nThanksForAllTheFish/rd03d/docs/superpowers/plans/2026-09-07-rd03d-case.md

# RD-03D + XIAO Fusion Case Implementation Plan

> **For agentic workers:** REQUIRED SUB-SKILL: Use superpowers:subagent-driven-development (recommended) or superpowers:executing-plans to implement this plan task-by-task. Steps use checkbox (`- [ ]`) syntax for tracking.

**Goal:** Build the two-part snap-fit case (adhesive back plate + front shell with radar window and USB notch) as a native parametric design in the user's running Fusion 360, verified against the imported real board models, with STLs exported to the repo.

**Architecture:** A small MCP driver (`run_fusion.py`) sends Fusion-API Python scripts to the local Fusion MCP server (`http://127.0.0.1:27182/mcp`) and fetches viewport screenshots. Numbered build scripts create user parameters, the BackPlate component, the FrontShell component, import + position the board STEPs, run interference checks, and export STLs. Every geometry stage is verified by reading back measurements AND by viewing a screenshot (the implementer Reads the PNG — actually look at it).

**Tech Stack:** Fusion 360 API (adsk.core/adsk.fusion) over Autodesk's MCP adapter; Python stdlib driver (urllib, no deps).

**Spec:** `docs/superpowers/specs/2026-09-06-rd03d-case-design.md`

---

## Standing rules for every task in this plan

- **Sequential, single implementer.** All tasks mutate ONE live Fusion document; never parallelize.
- **Prescriptive vs adaptable:** dimensions, user parameters, feature intent, component names, and verification criteria are prescriptive. Exact Fusion API calls are the starting point — if Fusion rejects a call, consult the API docs (`fusion_mcp_read` queryType `apiDocumentation`) and adapt, keeping intent identical. Record every adaptation in your report.
- **Idempotency:** scripts guard against re-runs (check for existing parameter/component by name; delete-and-rebuild a component rather than duplicating it). If a script half-fails, fix and re-run the same script.
- **Verify visually:** after each geometry script, capture screenshots (`run_fusion.py screenshot ...`, saved under the scratchpad) and READ the image files — confirm the geometry actually looks like the design, don't just trust `success: true`.
- **Fusion API unit trap:** the API's internal length unit is **cm**. User parameters are declared in mm; `param.value` returns cm. All raw `Point3D`/extrude distances in scripts must be in cm (the scripts read `param.value` so they stay consistent — never hardcode a mm number into a Point3D).
- **Units of trust:** the design is in the user's Fusion — they can watch. Do not save/close/discard their documents; do not touch other open documents; never call `doc.close`. Saving is the user's step at the end.
- Scratchpad for screenshots: `/private/tmp/claude-501/-path-to-rd03d/1a58ef3a-b659-4aae-a07a-3f6d1a6f573b/scratchpad/case/` (create it).
- Repo working dir: /path/to/rd03d, branch `feature/rd03d-case`.
- End every commit message with:
  `Co-Authored-By: Claude Fable 5 <noreply@anthropic.com>`

## Geometry reference (all mm; origin = interior center of the case, +Z out of the wall)

- Interior: `intW`=42 × `intH`=46 × `intD`=14. Back plate face at z=0 (plate body −2..0); shell front inner face at z=14, outer at 16.
- Shell outer: 46 × 50 × 18 (wraps the plate rim: shell walls run z=−2..16).
- RD-03D bay (left): board 15.1×44.0×6.35 lying long-axis vertical, patch side facing +Z, centered at x=−11.5, y=0; board back face rests on two crossbar supports at z=6.65 so the patch face sits at z=13 (1 mm behind the front inner wall). Perimeter fence (1.5 thick, to z=11) around footprint+`boardClear`.
- XIAO bay (right): board 22.5×17.8 centered at x=+8.0, y=0 (long axis along X), USB-C pointing +X; four 3×3 corner posts `postH`=3 tall; perimeter fence to z=5 with a full opening on the +X side for the USB. Wire channel is the ~5 mm gap between the two fences.
- Radar window: front wall pocket (from outside face z=16, depth `wall`−`windowT`=0.8) over the patch end: rect x∈[−11.5−9.5, −11.5+9.5], y∈[+1, +25] (covers the top ~22 mm of the stick + margin; if board orientation checks in Task 5 show patches at −Y, mirror the window and record it).
- USB notch: through the +X wall (x∈[21,23]), from the back rim z=−2 up to z=8, width y∈[−5.7,+5.7] (10.5 plug + 2·`usbClear` ≈ 11.3).
- Snap fit: four bumps on the shell's inner ±X walls (`snapBump`=0.5 proud, 6 long, z −1.6..−0.4, crest at x=±20.5) at y=±12; the plate's ±X edges get matching 6.2-wide, 0.6-deep BLIND pockets at y=±12 spanning z −1.7..−0.3 only — material ledges above and below each pocket retain the bumps axially (0.1 z-slop per side). Plate outline = 41.7×45.7 (interior − 2·`rimGap`).
- Tape recess: plate rear face (z=−2) pocket 34×38×0.6 centered.

---

### Task 1: MCP driver + connectivity smoke test

**Files:**
- Create: `case/fusion_scripts/run_fusion.py`
- Create: `case/fusion_scripts/00_smoke.py`

- [x] **Step 1: Write the driver**

`case/fusion_scripts/run_fusion.py`:

```python
#!/usr/bin/env python3
"""Send a Fusion API script to the local Fusion MCP server, or grab a screenshot.

Usage:
  run_fusion.py script <file.py> [--read-only]
  run_fusion.py screenshot <out.png> [direction]
"""
import base64
import json
import sys
import urllib.request

URL = "http://127.0.0.1:27182/mcp"

def rpc(session, payload):
    headers = {"Content-Type": "application/json",
               "Accept": "application/json, text/event-stream"}
    if session:
        headers["MCP-Session-Id"] = session
    req = urllib.request.Request(URL, data=json.dumps(payload).encode(),
                                 headers=headers)
    with urllib.request.urlopen(req, timeout=300) as r:
        sid = r.headers.get("MCP-Session-Id", session)
        body = r.read().decode()
    return sid, (json.loads(body) if body.strip() else None)

def connect():
    sid, _ = rpc(None, {"jsonrpc": "2.0", "id": 1, "method": "initialize",
                        "params": {"protocolVersion": "2025-03-26",
                                   "capabilities": {},
                                   "clientInfo": {"name": "rd03d-case-builder",
                                                  "version": "1.0"}}})
    rpc(sid, {"jsonrpc": "2.0", "method": "notifications/initialized"})
    return sid

def call(sid, name, args):
    _, resp = rpc(sid, {"jsonrpc": "2.0", "id": 2, "method": "tools/call",
                        "params": {"name": name, "arguments": args}})
    if resp is None:
        raise SystemExit("empty MCP response")
    if "error" in resp:
        raise SystemExit(f"MCP error: {resp['error']}")
    return resp["result"].get("content", [])

def main():
    if len(sys.argv) < 3:
        raise SystemExit(__doc__)
    mode = sys.argv[1]
    sid = connect()

    if mode == "script":
        src = open(sys.argv[2]).read()
        obj = {"script": src}
        if "--read-only" in sys.argv:
            obj["readOnly"] = True
        content = call(sid, "fusion_mcp_execute",
                       {"featureType": "script", "object": obj})
        ok = True
        for c in content:
            if c.get("type") != "text":
                continue
            try:
                d = json.loads(c["text"])
                print(d.get("message", c["text"]))
                if d.get("success") is False:
                    ok = False
            except json.JSONDecodeError:
                print(c["text"])
        sys.exit(0 if ok else 1)

    if mode == "screenshot":
        out = sys.argv[2]
        args = {"queryType": "screenshot", "width": 1200, "height": 900}
        if len(sys.argv) > 3 and not sys.argv[3].startswith("--"):
            args["direction"] = sys.argv[3]
        content = call(sid, "fusion_mcp_read", args)
        for c in content:
            if c.get("type") == "image" and c.get("data"):
                open(out, "wb").write(base64.b64decode(c["data"]))
                print("saved", out)
                return
            if c.get("type") == "text":
                try:
                    d = json.loads(c["text"])
                    img = d.get("imageData") or d.get("data")
                    if img:
                        open(out, "wb").write(base64.b64decode(img))
                        print("saved", out)
                        return
                    print(c["text"][:400])
                except json.JSONDecodeError:
                    print(c["text"][:400])
        raise SystemExit("no image in response")

    raise SystemExit(__doc__)

if __name__ == "__main__":
    main()
```

(If the screenshot response format differs from both handled shapes, print the
raw content once, adapt the parser, and record the deviation.)

- [x] **Step 2: Write the smoke script**

`case/fusion_scripts/00_smoke.py`:

```python
import adsk.core

def run(_context: str):
    app = adsk.core.Application.get()
    print("Fusion", app.version)
    doc = app.activeDocument
    print("active doc:", doc.name if doc else None)
    print("open docs:", app.documents.count)
```

- [x] **Step 3: Run it**

```bash
cd case/fusion_scripts && python3 run_fusion.py script 00_smoke.py --read-only
```

Expected: `Fusion 2705...` + active doc info, exit 0. (If connection refused: Fusion or its MCP add-in isn't running — report BLOCKED, the user must have Fusion open.)

- [x] **Step 4: Commit**

```bash
git add case/fusion_scripts/run_fusion.py case/fusion_scripts/00_smoke.py
git commit -m "feat(case): Fusion MCP driver and smoke test"
```

---

### Task 2: Document + user parameters

**Files:**
- Create: `case/fusion_scripts/01_setup.py`

- [x] **Step 1: Write the setup script**

`case/fusion_scripts/01_setup.py`:

```python
import adsk.core
import adsk.fusion

PARAMS = [
    ("wall", "2 mm", "shell wall thickness"),
    ("windowT", "1.2 mm", "radar window remaining thickness"),
    ("boardClear", "0.25 mm", "clearance around boards"),
    ("usbClear", "0.4 mm", "USB cutout clearance"),
    ("tapeRecess", "0.6 mm", "adhesive tape recess depth"),
    ("backT", "2 mm", "back plate thickness"),
    ("intW", "42 mm", "interior width"),
    ("intH", "46 mm", "interior height"),
    ("intD", "14 mm", "interior depth"),
    ("rimGap", "0.15 mm", "plate-to-shell fit gap per side"),
    ("snapBump", "0.5 mm", "snap bump proudness"),
    ("radarW", "15.1 mm", "RD-03D board width"),
    ("radarH", "44.0 mm", "RD-03D board length"),
    ("radarT", "6.35 mm", "RD-03D thickness incl rear connector"),
    ("radarCx", "-11.5 mm", "radar bay center X"),
    ("xiaoW", "22.5 mm", "XIAO width incl USB overhang"),
    ("xiaoH", "17.8 mm", "XIAO depth"),
    ("xiaoCx", "8.0 mm", "XIAO bay center X"),
    ("postH", "3 mm", "XIAO post height"),
]

def run(_context: str):
    app = adsk.core.Application.get()
    des = adsk.fusion.Design.cast(app.activeProduct) if app.activeProduct else None
    if des is None:
        doc = app.documents.add(adsk.core.DocumentTypes.FusionDesignDocumentType)
        des = adsk.fusion.Design.cast(app.activeProduct)
        print("created new design document:", doc.name)
    elif (des.userParameters.itemByName("wall") is None
          and (des.rootComponent.occurrences.count > 0
               or des.rootComponent.bRepBodies.count > 0)):
        raise RuntimeError("active design has other content and no case "
                           "params - not hijacking it; ask the controller")
    des.designType = adsk.fusion.DesignTypes.ParametricDesignType
    ups = des.userParameters
    for name, expr, comment in PARAMS:
        p = ups.itemByName(name)
        if p is None:
            ups.add(name, adsk.core.ValueInput.createByString(expr), "mm", comment)
            print("added", name, "=", expr)
        else:
            print("exists", name, "=", p.expression)
    print("user params total:", ups.count)
```

(Note: if a design document is already active with OTHER user content, do NOT
hijack it — check with the controller. A fresh/empty active design or none at
all are the expected states.)

- [x] **Step 2: Run and verify**

```bash
cd case/fusion_scripts && python3 run_fusion.py script 01_setup.py
```

Expected: `created new design document` (or all-exists on rerun) + 19 params added. Verify by re-running with `--read-only`? No — instead run a quick read-only param dump (inline scratch script printing every `ups.item(i).name/.expression`) and confirm all 19 match the table.

- [x] **Step 3: Commit**

```bash
git add case/fusion_scripts/01_setup.py
git commit -m "feat(case): Fusion design document and user parameters"
```

---

### Task 3: BackPlate component

**Files:**
- Create: `case/fusion_scripts/02_backplate.py`

- [x] **Step 1: Write the script**

`case/fusion_scripts/02_backplate.py` — intent (prescriptive) and starting code. The component named `BackPlate` under the root, containing:
1. Plate: rectangle (intW−2·rimGap) × (intH−2·rimGap) centered on origin, extruded z=−backT..0.
2. Tape recess: 34×38 pocket, 0.6 deep, cut into the z=−backT face.
3. Snap grooves: on each ±X edge at y=±12, a 6.2 wide × 0.6 deep groove through the plate thickness (cut from the edge inward).
4. Radar bay on the +Z face: perimeter fence 1.5 thick around (radarW+2·boardClear) × (radarH+2·boardClear) centered at (radarCx, 0), fence from z=0 to z=11; two crossbar supports 4 wide spanning the bay interior at y=±18, z=0..6.65 (board back rests on them → patch face lands at z=13).
5. XIAO bay: four 3×3 posts (z=0..postH) at the corners of (xiaoW−2)×(xiaoH−2) centered at (xiaoCx, 0); perimeter fence 1.5 thick, z=0..5, around (xiaoW+2·boardClear)×(xiaoH+2·boardClear), with the +X side of the fence OMITTED (USB cable path).

```python
import adsk.core
import adsk.fusion

def p(des, name):
    return des.userParameters.itemByName(name).value  # cm

def rect(sk, cx, cy, w, h):
    sk.sketchCurves.sketchLines.addTwoPointRectangle(
        adsk.core.Point3D.create(cx - w / 2, cy - h / 2, 0),
        adsk.core.Point3D.create(cx + w / 2, cy + h / 2, 0))

def extrude(comp, profiles, z0, z1, op):
    ext = comp.features.extrudeFeatures
    inp = ext.createInput(profiles, op)
    start = adsk.fusion.OffsetStartDefinition.create(
        adsk.core.ValueInput.createByReal(z0))
    inp.startExtent = start
    inp.setOneSideExtent(
        adsk.fusion.DistanceExtentDefinition.create(
            adsk.core.ValueInput.createByReal(z1 - z0)),
        adsk.fusion.ExtentDirections.PositiveExtentDirection)
    return ext.add(inp)

def collection(items):
    coll = adsk.core.ObjectCollection.create()
    for i in items:
        coll.add(i)
    return coll

def run(_context: str):
    app = adsk.core.Application.get()
    des = adsk.fusion.Design.cast(app.activeProduct)
    root = des.rootComponent

    for occ in list(root.occurrences):
        if occ.component.name == "BackPlate":
            occ.deleteMe()
            print("removed existing BackPlate")

    occ = root.occurrences.addNewComponent(adsk.core.Matrix3D.create())
    comp = occ.component
    comp.name = "BackPlate"

    intW, intH = p(des, "intW"), p(des, "intH")
    backT, rimGap = p(des, "backT"), p(des, "rimGap")
    tape = p(des, "tapeRecess")
    rW, rH, rT = p(des, "radarW"), p(des, "radarH"), p(des, "radarT")
    rCx = p(des, "radarCx")
    xW, xH, xCx = p(des, "xiaoW"), p(des, "xiaoH"), p(des, "xiaoCx")
    postH, clear = p(des, "postH"), p(des, "boardClear")
    intD, wall, winT = p(des, "intD"), p(des, "wall"), p(des, "windowT")
    MM = 0.1

    # 1. plate
    sk = comp.sketches.add(comp.xYConstructionPlane)
    rect(sk, 0, 0, intW - 2 * rimGap, intH - 2 * rimGap)
    extrude(comp, sk.profiles.item(0), -backT, 0,
            adsk.fusion.FeatureOperations.NewBodyFeatureOperation)
    print("plate ok")

    # 2. tape recess (cut upward from below)
    sk = comp.sketches.add(comp.xYConstructionPlane)
    rect(sk, 0, 0, 34 * MM, 38 * MM)
    extrude(comp, sk.profiles.item(0), -backT, -backT + tape,
            adsk.fusion.FeatureOperations.CutFeatureOperation)
    print("tape recess ok")

    # 3. snap grooves at plate +/-X edges, y=+/-12
    sk = comp.sketches.add(comp.xYConstructionPlane)
    for sx in (-1, 1):
        edge = sx * (intW / 2 - rimGap)
        for sy in (-1, 1):
            rect(sk, edge - sx * 0.03, sy * 12 * MM, 0.12, 6.2 * MM)
    profs = collection([sk.profiles.item(i) for i in range(sk.profiles.count)])
    extrude(comp, profs, -backT, 0,
            adsk.fusion.FeatureOperations.CutFeatureOperation)
    print("snap grooves ok")

    # 4. radar bay: fence ring + crossbars
    bayW, bayH = rW + 2 * clear, rH + 2 * clear
    sk = comp.sketches.add(comp.xYConstructionPlane)
    rect(sk, rCx, 0, bayW + 2 * 1.5 * MM, bayH + 2 * 1.5 * MM)
    rect(sk, rCx, 0, bayW, bayH)
    ring = None
    for i in range(sk.profiles.count):
        pr = sk.profiles.item(i)
        if pr.profileLoops.count == 2:
            ring = pr
    extrude(comp, ring, 0, 11 * MM,
            adsk.fusion.FeatureOperations.JoinFeatureOperation)
    sk = comp.sketches.add(comp.xYConstructionPlane)
    for sy in (-1, 1):
        rect(sk, rCx, sy * 18 * MM, bayW, 4 * MM)
    profs = collection([sk.profiles.item(i) for i in range(sk.profiles.count)])
    board_back_z = intD - 1 * MM - rT  # patch face lands 1mm behind front wall
    extrude(comp, profs, 0, board_back_z,
            adsk.fusion.FeatureOperations.JoinFeatureOperation)
    print("radar bay ok, support top z(cm)=", round(board_back_z, 3))

    # 5. xiao bay: 4 posts + 3-sided fence (open toward +X)
    sk = comp.sketches.add(comp.xYConstructionPlane)
    for sx in (-1, 1):
        for sy in (-1, 1):
            rect(sk, xCx + sx * (xW / 2 - 1.5 * MM),
                 sy * (xH / 2 - 1.5 * MM), 3 * MM, 3 * MM)
    profs = collection([sk.profiles.item(i) for i in range(sk.profiles.count)])
    extrude(comp, profs, 0, postH,
            adsk.fusion.FeatureOperations.JoinFeatureOperation)
    fW, fH = xW + 2 * clear, xH + 2 * clear
    t = 1.5 * MM
    sk = comp.sketches.add(comp.xYConstructionPlane)
    rect(sk, xCx - fW / 2 - t / 2, 0, t, fH + 2 * t)          # -X side
    rect(sk, xCx, fH / 2 + t / 2, fW + 2 * t, t)              # +Y side
    rect(sk, xCx, -(fH / 2 + t / 2), fW + 2 * t, t)           # -Y side
    profs = collection([sk.profiles.item(i) for i in range(sk.profiles.count)])
    extrude(comp, profs, 0, 5 * MM,
            adsk.fusion.FeatureOperations.JoinFeatureOperation)
    print("xiao bay ok")

    print("BackPlate bodies:", comp.bRepBodies.count)
```

- [x] **Step 2: Run, verify, iterate**

```bash
cd case/fusion_scripts && python3 run_fusion.py script 02_backplate.py
```

Iterate on API errors per the standing rules. When it succeeds:

```bash
SPC=/private/tmp/claude-501/-path-to-rd03d/1a58ef3a-b659-4aae-a07a-3f6d1a6f573b/scratchpad/case
mkdir -p $SPC
python3 run_fusion.py screenshot $SPC/02_iso.png
python3 run_fusion.py screenshot $SPC/02_top.png top
```

READ both PNGs. Confirm: one plate with tape recess underneath, tall radar fence ring left with two crossbars, XIAO posts + 3-sided fence right, snap grooves on the ±X edges. Also run a read-only scratch script printing the component's bounding box and body count; plate bbox must be ≈41.7 × 45.7 × (2 + 11 fence) mm.

- [x] **Step 3: Commit**

```bash
git add case/fusion_scripts/02_backplate.py
git commit -m "feat(case): BackPlate component with board bays and snap grooves"
```

---

### Task 4: FrontShell component

**Files:**
- Create: `case/fusion_scripts/03_shell.py`

- [x] **Step 1: Write the script**

`case/fusion_scripts/03_shell.py` — intent (prescriptive): component `FrontShell` containing:
1. Outer box (intW+2·wall) × (intH+2·wall), z=−backT..intD+wall.
2. Cavity cut: intW × intH, z=−backT..intD (leaves the front wall `wall` thick and side walls wrapping the plate rim).
3. Radar window pocket: on the outer front face (z=intD+wall), rect x∈[radarCx−9.5 mm, radarCx+9.5 mm], y∈[1 mm, 25 mm], cut depth (wall−windowT) → remaining wall = windowT.
4. USB notch: cut through the +X wall, x∈[intW/2, intW/2+wall], y∈[−5.65 mm, +5.65 mm], z∈[−backT, 8 mm].
5. Snap bumps: on the inner faces of the ±X walls at y=±12, z centered −1 mm: bumps 6 long (Y), snapBump proud (X), 1.2 tall (Z), as small joined boxes with chamfered/rounded lead-in if convenient (plain boxes acceptable v1).

Starting code — reuse the helper functions from `02_backplate.py` verbatim (`p`, `rect`, `extrude`, `collection`; copy them into this file), then:

```python
def run(_context: str):
    app = adsk.core.Application.get()
    des = adsk.fusion.Design.cast(app.activeProduct)
    root = des.rootComponent

    for occ in list(root.occurrences):
        if occ.component.name == "FrontShell":
            occ.deleteMe()
            print("removed existing FrontShell")

    occ = root.occurrences.addNewComponent(adsk.core.Matrix3D.create())
    comp = occ.component
    comp.name = "FrontShell"

    intW, intH, intD = p(des, "intW"), p(des, "intH"), p(des, "intD")
    wall, backT = p(des, "wall"), p(des, "backT")
    winT, rCx = p(des, "windowT"), p(des, "radarCx")
    MM = 0.1

    # 1+2: outer box then cavity
    sk = comp.sketches.add(comp.xYConstructionPlane)
    rect(sk, 0, 0, intW + 2 * wall, intH + 2 * wall)
    extrude(comp, sk.profiles.item(0), -backT, intD + wall,
            adsk.fusion.FeatureOperations.NewBodyFeatureOperation)
    sk = comp.sketches.add(comp.xYConstructionPlane)
    rect(sk, 0, 0, intW, intH)
    extrude(comp, sk.profiles.item(0), -backT, intD,
            adsk.fusion.FeatureOperations.CutFeatureOperation)
    print("shell box ok")

    # 3: radar window pocket
    sk = comp.sketches.add(comp.xYConstructionPlane)
    rect(sk, rCx, 13 * MM, 19 * MM, 24 * MM)
    extrude(comp, sk.profiles.item(0), intD + winT, intD + wall,
            adsk.fusion.FeatureOperations.CutFeatureOperation)
    print("window ok")

    # 4: usb notch through +X wall
    sk = comp.sketches.add(comp.xYConstructionPlane)
    rect(sk, intW / 2 + wall / 2, 0, wall + 0.02, 11.3 * MM)
    extrude(comp, sk.profiles.item(0), -backT, 8 * MM,
            adsk.fusion.FeatureOperations.CutFeatureOperation)
    print("usb notch ok")

    # 5: snap bumps on inner +/-X walls
    snap = p(des, "snapBump")
    sk = comp.sketches.add(comp.xYConstructionPlane)
    for sx in (-1, 1):
        cx = sx * (intW / 2 - snap / 2)
        for sy in (-1, 1):
            rect(sk, cx, sy * 12 * MM, snap, 6 * MM)
    profs = collection([sk.profiles.item(i) for i in range(sk.profiles.count)])
    extrude(comp, profs, -1.6 * MM, -0.4 * MM,
            adsk.fusion.FeatureOperations.JoinFeatureOperation)
    print("snap bumps ok")
    print("FrontShell bodies:", comp.bRepBodies.count)
```

- [x] **Step 2: Run, verify, iterate**

Run the script; iterate on errors. Screenshots: iso + front + a look into the open back (`python3 run_fusion.py screenshot $SPC/03_back.png back` — adapt direction names to whatever the server accepts). READ the images: box with open back, thinned window pad visible on the front over the radar bay, USB notch in the right wall reaching the rim, four bumps inside near the back rim. Read-only measurement script: outer bbox ≈46 × 50 × 18 mm; confirm window pocket floor thickness = 1.2 (measure via body volume or a `measureManager.measureMinimumDistance` between window floor face and front outer face if convenient — otherwise assert extrude parameters and eyeball the screenshot).

As-built correction: every Cut here (and the bump Join) must set `inp.participantBodies` to the shell body — an unrestricted cut modifies every intersecting body in the design, and the cavity cut had hollowed the BackPlate body to zero volume (02's cuts/joins now pass the plate body as participant for the same cross-component robustness).

- [x] **Step 3: Commit**

```bash
git add case/fusion_scripts/03_shell.py
git commit -m "feat(case): FrontShell with radar window, USB notch, snap bumps"
```

---

### Task 5: Import boards, position, interference check

**Files:**
- Create: `case/fusion_scripts/04_boards.py`

- [x] **Step 1: Write the script**

Intent (prescriptive): import both STEP files as components into the design, orient/translate them into their bays (radar patch-side facing +Z at z_back=intD−1mm−radarT, XIAO on its posts at z=postH), then run interference analysis between every board and every case component; print each pair's interfering volume. The board STEPs' native orientations are unknown — the script prints each imported component's bounding box; the implementer adjusts the rotation matrix and re-runs until the bbox matches the expected footprint, THEN fine-tunes position. Screenshots at each attempt.

Starting code:

```python
import adsk.core
import adsk.fusion

RADAR = "/Users/me/Downloads/rd-03d-sensor-1/RD-03D.step"
XIAO = ("/Users/me/Downloads/seeed-studio-xiao-esp32-c6-1/"
        "Seeed Studio XIAO ESP32-C6.step")

def p(des, name):
    return des.userParameters.itemByName(name).value

def bbox_of(occ):
    bb = None
    for body in occ.bRepBodies:
        b = body.boundingBox
        if bb is None:
            bb = adsk.core.BoundingBox3D.create(b.minPoint.copy(), b.maxPoint.copy())
        else:
            bb.combine(b)
    return bb

def run(_context: str):
    app = adsk.core.Application.get()
    des = adsk.fusion.Design.cast(app.activeProduct)
    root = des.rootComponent

    for occ in list(root.occurrences):
        if occ.component.name.startswith(("RD-03D", "Seeed", "XIAO")):
            occ.deleteMe()
            print("removed prior import:", occ.name)

    imp = app.importManager
    before = root.occurrences.count
    imp.importToTarget(imp.createSTEPImportOptions(RADAR), root)
    radar_occ = root.occurrences.item(before)
    imp.importToTarget(imp.createSTEPImportOptions(XIAO), root)
    xiao_occ = root.occurrences.item(before + 1)

    for name, occ in (("radar", radar_occ), ("xiao", xiao_occ)):
        bb = bbox_of(occ)
        print(name, "bbox(cm): x %.2f..%.2f  y %.2f..%.2f  z %.2f..%.2f" %
              (bb.minPoint.x, bb.maxPoint.x, bb.minPoint.y, bb.maxPoint.y,
               bb.minPoint.z, bb.maxPoint.z))

    # TRANSFORMS: start with identity + translation to bay centers; the
    # implementer sets the rotation after reading the printed bboxes.
    # Target (cm): radar footprint 1.51 x 4.40, patch face at z = intD-0.1;
    #              xiao footprint 2.25 x 1.78 sitting at z = postH.
    intD, rT = p(des, "intD"), p(des, "radarT")
    rCx, xCx, postH = p(des, "radarCx"), p(des, "xiaoCx"), p(des, "postH")

    t = adsk.core.Matrix3D.create()
    t.translation = adsk.core.Vector3D.create(rCx, 0, intD - 0.1 - rT)
    radar_occ.transform2 = t
    t = adsk.core.Matrix3D.create()
    t.translation = adsk.core.Vector3D.create(xCx, 0, postH)
    xiao_occ.transform2 = t
    print("initial placement done - check bboxes/screenshots and refine")

    # Interference: boards vs case components
    ents = adsk.core.ObjectCollection.create()
    for occ in root.occurrences:
        for b in occ.bRepBodies:
            ents.add(b)
    inp = des.createInterferenceInput(ents)
    res = des.analyzeInterference(inp)
    if res.count == 0:
        print("INTERFERENCE: none")
    for i in range(res.count):
        r = res.item(i)
        print("INTERFERENCE: %.4f cm^3 between %s and %s" %
              (r.interferenceVolume, r.entityOne.parentComponent.name,
               r.entityTwo.parentComponent.name))
```

- [x] **Step 2: Iterate placement until verified**

Loop: run script → read printed bboxes → adjust the rotation/translation (`Matrix3D.setToRotation` about the right axis before setting translation) in the script → re-run → screenshot (`iso`, `front`, `right`) and READ them. Done when:
1. Radar bbox footprint ≈15.1 × 44 mm centered at (−11.5, 0), patch face toward +Z, front face at z≈13 mm.
2. XIAO bbox footprint ≈22.5 × 17.8 mm at (8, 0), top of USB below z≈8 mm, USB toward +X (visible in the notch on the `right` screenshot).
3. Interference report: **zero pairs** involving a board and a case part (tiny (<0.001 cm³) board-internal self-pairs from the vendor models may be ignored — report them).
4. Window judgment call: the screenshot must show the thinned window over the END OF THE STICK WHERE THE ANTENNA PATCHES ARE (patches = the 3 square pads on the board face; visible in the model). If they're at −Y, change the window sketch rect in `03_shell.py` to y∈[−25 mm, −1 mm], re-verify, and record the flip.

As-built corrections (Task 5):
- **Window NOT flipped.** The vendor STEP does not model the flat copper
  patches at all (the raised diamond on the front face is the radar IC,
  mounted at 45°, per the reference photo shipped next to the STEP). The
  real RD-03D has its 4-patch RX array at the end far from the 5-pin
  connector and 2 TX patches near the connector. `04_boards.py` rotates
  the board 180° about Z (`RADAR_FLIP180 = True`) so the connector end is
  at −Y and the RX array sits at +Y under the y∈[1,25] window as designed.
  The 2 TX patches at ~y −18..−5 radiate through the full 2 mm wall.
- **Radar fence notched (`02_backplate.py` step 4b).** The prescriptive
  bay centers leave only 0.72 mm between the boards (radar +X edge −3.95,
  XIAO −X edge −3.23), so the radar fence's +X wall (x −3.7..−2.2, 11
  tall) passed through the XIAO board. The wall is now cut away above
  z=postH over y ±9.4 (XIAO footprint + 0.5 clearance); the stub below
  stays co-planar with the posts and the wall segments beyond y ±9.4
  still retain the radar laterally. The spec's "~5 mm wire channel
  between the two fences" was never geometrically possible.
- API adaptation: `InterferenceResult` has no `interferenceVolume`
  property in this Fusion build; the script measures
  `interferenceBody.volume` instead.

- [x] **Step 3: Commit**

```bash
git add case/fusion_scripts/04_boards.py
git commit -m "feat(case): import boards, position in bays, interference-check"
```

---

### Task 6: Export STLs + README + handoff

**Files:**
- Create: `case/fusion_scripts/05_export.py`
- Create: `case/README.md`

- [x] **Step 1: Export script**

`case/fusion_scripts/05_export.py`:

```python
import adsk.core
import adsk.fusion

OUT = "/path/to/rd03d/case"

def run(_context: str):
    app = adsk.core.Application.get()
    des = adsk.fusion.Design.cast(app.activeProduct)
    root = des.rootComponent
    em = des.exportManager
    for comp_name, fname in (("BackPlate", "rd03d_case_back.stl"),
                             ("FrontShell", "rd03d_case_shell.stl")):
        occ = None
        for o in root.occurrences:
            if o.component.name == comp_name:
                occ = o
        if occ is None:
            raise RuntimeError("missing component " + comp_name)
        opts = em.createSTLExportOptions(occ, f"{OUT}/{fname}")
        opts.meshRefinement = adsk.fusion.MeshRefinementSettings.MeshRefinementHigh
        em.execute(opts)
        print("exported", fname)
```

Run it; confirm both STL files exist in `case/` and parse as well-formed binary STL. (As-built deviation: the plan's ">50 KB / >1000 triangles" heuristics don't apply to this all-planar geometry — actual 292 and 124 triangles; verification used byte-exact structure checks plus vertex bounding boxes matching the design dimensions, which is stronger.)

- [x] **Step 2: README**

`case/README.md`:

```markdown
# RD-03D + XIAO ESP32-C6 Case

Two-part snap-fit case designed natively in Fusion 360 (built via its MCP
API — the numbered scripts in `fusion_scripts/` are the construction record).
The living design is in your Fusion; save it to your own project.

## Parts

- `rd03d_case_back.stl` — back plate: adhesive face (tape recess) down,
  radar bay left, XIAO posts right.
- `rd03d_case_shell.stl` — front shell: 1.2 mm radar window, USB-C notch,
  four snap bumps engage the plate's edge grooves.

## Printing

PLA or PETG, 0.4 mm nozzle, 0.2 mm layers, no supports.
Back plate: print flat (adhesive face down). Shell: print open-side-up.

## Assembly

1. Wire the boards (radar TX→D7, RX→D6, 5V, GND), seat the RD-03D in its
   bay patch-side out, the XIAO on its posts with USB-C toward the notch.
2. Snap the shell on (bumps click into the plate grooves). Unclip with a
   fingernail in the USB notch.
3. Stick 3M VHB tape in the recessed back panel.

## Tweaking fit

Open the design in Fusion → Modify → Change Parameters. `boardClear`,
`rimGap`, and `snapBump` are the fit-critical ones; `windowT` is the radar
window thickness (keep ≤1.6 mm, no metal/foil in front of the radar).
Re-export STLs after edits (File → 3D Print, or re-run
`fusion_scripts/05_export.py` via `run_fusion.py`).
```

- [x] **Step 3: Final screenshots for the record + commit**

Capture final `iso` and `front` screenshots into the scratchpad, READ them one last time (assembled case with boards visible through nothing — shell on), then:

```bash
git add case/fusion_scripts/05_export.py case/README.md case/rd03d_case_back.stl case/rd03d_case_shell.stl
git commit -m "feat(case): export print STLs and document the case"
```

- [ ] **Step 4: User handoff (user-owned, report pending)**

The user: eyeballs the design in Fusion (it's open on their screen), saves it
to their project (File → Save), optionally tweaks parameters, prints both
parts, and test-fits the boards. Any fit corrections = parameter change +
re-export.

---

## Change request (2026-09-07): LEGO Technic mount

Implemented per the spec's revised Mounting bullet.

- **`01_setup.py`:** `backT` 2 mm → 8 mm; four new params: `legoPitch`
  8 mm, `legoHole` 4.9 mm (Technic pin hole dia, FDM-calibrated),
  `legoCbDia` 6.4 mm, `legoCbDepth` 0.9 mm (23 params total). The script
  now also updates an existing parameter whose expression differs from
  the table (prints "updated name old -> new") instead of leaving it.
- **`02_backplate.py`:** new step 7 (participants=[plate_body]): six
  ⌀`legoHole` through-holes (z −backT..0) on the exact 8 mm LEGO pitch —
  centers (mm) (0.95, −12), (0.95, −4), (0.95, +4), (0.95, +12),
  (8.95, −4), (8.95, +4) — each counterbored ⌀`legoCbDia` × `legoCbDepth`
  on BOTH faces, plus a 0.3 mm 45° entry chamfer on all six rear bore
  openings (ChamferFeatures accepted the edge set on the first try; the
  edges are found by Circle3D radius ≈ legoHole/2 at z = −backT +
  legoCbDepth, since the rear counterbore relocates the bore's entry
  edge there).
- **`03_shell.py`: no edits needed** — everything derives from `backT`.
  Verified live after the re-run, not assumed: shell bbox 46 × 50,
  z −8..16; USB notch void probed OUTSIDE at z −7.5 (new rim) and 7.5,
  wall INSIDE above/beside; snap bumps probed INSIDE at z −1.0 /
  OUTSIDE at −2.0 and +0.2 (still z −1.6..−0.4, engaging the plate
  pockets near its front face).
- Boards did not move (absolute transforms): radar z 6.65..13, XIAO
  z 3.00..7.46, footprints unchanged. Interference re-run over all 40
  bodies (now including the XIAO STEP's nested sub-bodies): zero
  board–case and case–case pairs; the only pairs are tiny (≤0.0008 cm³)
  vendor-model self-intersections inside the XIAO assembly.
- Plate probes all passed: bore void at each center (z −4), wall INSIDE
  at center+3 mm, rear counterbore ring OUTSIDE at z −7.25 (below the
  −7.1 cb floor, above the −7.4 tape-recess floor — the discriminating
  probe), INSIDE at −7.05, front counterbore OUTSIDE at −0.45. Adjacent
  hole spacing exactly 8.0 mm.
- STLs re-exported: plate z now −8..11 (19 mm), 292 → 3572 triangles
  (tessellated bores/counterbores/chamfers); shell 124 triangles,
  z −8..16.
- Note: the rear counterbores (z −8..−7.1) overlap the 0.6 mm tape
  recess (floor −7.4) since all six holes sit inside the recess
  footprint — they effectively deepen it locally by 0.3 mm; pin collars
  still seat on the counterbore floor as intended. The fence bars at
  y ±9.15..10.65 slightly overhang the (0.95, ±12) hole openings at
  z>0 on one edge (~1 mm of rim); pin tips still have most of the front
  counterbore free to click into.

**2026-09-07: exterior edge softening.** Three new params (26 total):
`cornerFillet` 2.5 mm, `frontChamfer` 1 mm, `softFillet` 0.8 mm.
`03_shell.py` gained a final "soften exterior edges" step on the shell
body only, applied in order: (a) the 4 outer vertical corner edges
filleted r=2.5; (b) front-face (z=16) outer perimeter chamfered 1 mm —
found 8 edges after the corner fillets, not the drawn 9, because the
window pocket touches the y=+25 outer face and its x=−21 wall sits only
2 mm from the corner, so the r=2.5 fillet consumes that short segment
and leaves the perimeter chain open against the pocket wall. The single
8-edge chamfer feature is refused by the kernel (ASM_BL_CAP_COMPLEX at
that open end: the 1 mm chamfer would dip below the 0.8 mm pocket
floor), and per-edge chamfers fail on all four arcs (END_TOO_CMPLX), so
the script chamfers 7 edges as one feature and then attempts the
pocket-adjacent arc separately — in practice the 7-edge feature's
termination rolls over that arc too, leaving no z=16 arc edge behind;
a probe at (−22.23, 24.23, 15.95) confirms the corner IS chamfered
(reported as "7/8" by the count guard; the corner arc's chamfer had
reduced depth at its mid-angle rather than the full 1 mm — moot after
the 2026-09-07 interior-pocket flip below); (c)
back-rim (z=−8) outer perimeter filleted r=0.8 on 9 edges (the USB
notch splits the +X segment); (d) USB-notch outer edges (two verticals
at x=23, y=±5.65 and the outer top edge at z=8) filleted r=0.8, 3/3, no
skips. Verified live: shell still 1 body, bbox unchanged 46×50, z
−8..16; probes (22.9, 24.9, 4) OUT / (22, 24, 4) IN (corner), (22.9, 0,
15.9) OUT / (22.9, 0, 14.5) IN (chamfer), (22.95, 15, −7.95) OUT /
(22.5, 15, −7.5) IN (rim — probed clear of the USB notch, where a y=0
probe would be vacuously OUT),
(20.7, 12, −1.0) IN (snap bump), window pocket/pane probes unchanged;
BackPlate volume identical before/after (16.41250 cm³) and its STL
byte-identical (same SHA-1); boards unmoved; interference re-run over
40 bodies: zero board–case and case–case pairs (only the known tiny
XIAO vendor-model self-pairs). Shell STL re-exported: 124 → 2312
triangles (tessellated fillet/chamfer surfaces).

**2026-09-07: window pocket flipped to interior (user design review)** —
smooth exterior, no bed-side bridge, front chamfer now a clean 8-edge
loop (mid-arc thinning resolved). `03_shell.py` step 3 now cuts the
pocket from the cavity's front face: z intD..intD+(wall−windowT)
(14..14.8), leaving the 1.2 mm window panel at z 14.8..16 with the
outer front face fully flat; all the pocket-adjacent chamfer
special-casing (7-edge group + roll-over handling) is deleted and the
front perimeter is chamfered as one feature with a strict count guard
== 8. Deviation: the pocket's +Y extent is clamped from 25 to 23 mm
(intH/2) — on the interior side, cutting past the cavity edge would
tunnel through the solid top wall and open a 19 × 0.8 mm slot on the
outer +Y face (there is no front wall to thin beyond y=23 anyway).
Verified live: shell 1 body, bbox unchanged 46 × 50, z −8..16, volume
11.7421 → 11.7628 cm³ (+0.021: mostly the 2 mm pocket clamp, minus the
now-full-depth corner chamfer); probes (−11.5, 13, 15.6) IN (old
exterior pocket zone now solid, was OUT), (−11.5, 13, 14.4) OUT
(interior pocket void, was wall), (−11.5, 13, 15.4) and (14.9) IN
(window panel), (−22.2, 24.2, 15.3) OUT / (−21.8, 23.8, 15.3) IN
(full-depth chamfer at the previously-thin corner), (−11.5, 24.5,
14.4) IN (top wall intact — no slot), (−11.5, 22.5, 14.4) OUT (pocket
reaches the cavity edge); rim/snap probes unchanged. Radar patch face
(z=13) to window panel gap now 1.8 mm over the pocket. Interference
over 40 bodies: zero board–case and case–case pairs. BackPlate volume
and STL untouched; shell STL re-exported (2312 triangles — flat front
loses facets, interior pocket adds them).

**2026-09-07: thin-wall fix for 0.6 mm nozzles — plate ±Y fence walls
removed, shell retention ribs added (user print failure report).** The
back plate's radar-fence ±Y segments were only 0.6 mm thick after the
plate-outline trim and failed to print on a 0.6 mm nozzle.
`02_backplate.py` step 4 now extrudes just the two 1.5 mm ±X side walls
(full old ring Y-span, still trimmed to the plate outline) plus the
unchanged crossbars — no ±Y wall segments exist anywhere.
`03_shell.py` gained step 4b: two radar retention ribs joined to the ±Y
cavity walls (x −19.3..−3.7 = radarCx ± bayW/2, inner faces at
y = ±22.26 = ±(intH/2 − 0.74 mm), z 6..14; rects extend 0.5 mm into
the walls so the Join merges). Rib inner faces vs board edges ±22.01
→ 0.25 mm clearance per side with the lid on; rib top face is coplanar
with the interior window-pocket floor (z=14) and the rib X ends are
coplanar with the plate fence walls' inner faces — no volume overlaps
(interference re-run over 40 bodies: zero board–case and case–case
pairs). Verified live: plate 16.4125 → 16.2066 cm³ (−0.206, exactly
2 × 0.6×15.6×11 mm walls), shell 11.7628 → 11.9475 cm³ (+0.185,
exactly 2 × 0.74×15.6×8 mm ribs); probes (−11.5, ±22.5, 5) now OUTSIDE
the plate (old wall zone y 22.25..22.85 void), ±X walls and crossbars
still INSIDE, shell ribs INSIDE at (−11.5, ±22.6, 10) and OUTSIDE at
(−11.5, 22.0, 10) / (−11.5, 22.6, 5); boards unmoved. Both STLs
re-exported (plate 3572 triangles z −8..11, shell 2344 z −8..16).
Quirk found: deleting a component leaves its name reserved in the
document's name registry until save, so a delete-and-rebuild gets
suffixed "BackPlate (1)"; both scripts now rename the old component
to `*_deleted` before deleting, and `05_export.py` matches component
names by prefix. The live components carry the "(1)" suffix until the
user's next save + rebuild (cosmetic only).

**2026-09-07: tape recess deleted (flat first layer, user print
report); rib end clearance + self-centering chamfer.** With the LEGO
Technic holes as the primary mount, the 34×38×0.6 rear tape recess only
hurt printability: back-face-down the first layer contacted just the
outer rim, then bridged the whole 34×38 span. `02_backplate.py` step 2
is deleted — the rear face is now fully flat (tape sticks directly to
it); the rear Technic counterbores (0.9 deep) and their 0.3 mm entry
chamfers are unchanged. The `tapeRecess` user parameter remains in
`01_setup.py`/the live doc but is now unused. Plate volume 16.2066 →
16.86597 cm³ (+0.65937 = the 775.2 mm³ recess minus the 115.8 mm³
already removed by the six rear counterbores, which all sat inside the
recess footprint). `03_shell.py` step 4b: each retention rib shortened
0.3 mm per X end (span bayW − 0.6 = 15.0 mm, x −19.0..−4.0, still
centered on radarCx) so the lid doesn't force-fit against the plate's
fence walls (was coplanar). New step 4c: 45° self-centering lead-in
chamfer on each rib's lower-inner edge (z=6, y=±22.26). The prescribed
0.8 mm is refused by the kernel (ASM_BL_UNFIN_SHEET — the rib is only
0.74 mm thick, so the chamfer's horizontal leg overruns the bottom
face into the concave wall corner at y=±23); the script falls back to
0.6 mm equal-distance (applied cleanly, 0.14 mm of bottom face left —
intent preserved, adaptation recorded). Shell volume 11.9475 →
11.93501 cm³ (−0.01249 = 7.1 mm³ rib ends + 5.4 mm³ chamfers).
Verified live, 30/30 probes: (0,0,−7.9) and (0,0,−7.7) now INSIDE the
plate (old recess void), rear cb ring (3.75,−12,−7.5) OUTSIDE /
(…,−7.05) INSIDE, bores/front cbs/snap pockets/bays intact; rib
(−19.15, 22.6, 10) OUTSIDE / (−18.9, …) INSIDE (both ends, both ribs);
chamfer (−11.5, ±22.35, 6.2) OUTSIDE (dy+dz 0.29 < 0.6) and
(−11.5, 22.35, 6.6) INSIDE (0.69 > 0.6 — proves 0.6, not 0.8);
window/USB/snap-bump probes unchanged. Boards unmoved (radar z
6.65..13, XIAO z 3.00..7.46); interference over 40 bodies: zero
board–case and case–case pairs. STLs re-exported: plate 3572 → 3556
triangles (z −8..11), shell 2344 → 2352 (z −8..16). README: nozzle
line now 0.4–0.6 mm, tape-recess bridging note deleted, Parts/Assembly
now describe the flat back with direct-stick VHB as the adhesive
option. (The Geometry reference above still lists the original tape
recess; per the established pattern it is corrected by this entry, not
edited in place.)

**2026-09-07: board seating fix (crossbars bear on PCB at z=10.46, not on
the connector), TX window added (all 6 patches), XIAO hold-down boss.**
Three approved design fixes in one commit; branch `fix/case-board-seating`.

*Measurement provenance* (probed on the live vendor solids, not derived):
RD-03D rear profile with the board front face at z=13.0 (board spans
x −19.05..−3.95, y ±22.01) — the 5-pin connector protrudes rearward to
z=6.70 over y −20..−13.5 in the middle columns and must NOT be loaded;
the bare PCB rear face is flat and consistent; full-board-width
component-free bands at that face verified across x −18.6, −17, −14,
−11.5, −9, −6, −4.4 are **y −13.0…−11.0** and **y +17.5…+20.0**. XIAO top
profile (board z 3.00..7.46, x −3.23..19.23, y ±8.89) — RF shield can is a
flat plateau at z=6.20 over about x +0.5…+11.5, y −6…+6; the USB-C
connector is taller at z=7.40 over x +13…+17.

- **`02_backplate.py` step 4 (change 1).** The two 4 mm crossbars at
  y=±18 with tops at `intD − 1 − radarT` = 6.65 mm were wrong in both
  places: 6.65 is the board's TOTAL thickness *including* the rear
  connector, so the +18 bar stopped 3.85 mm short of the board entirely
  and the −18 bar was the sole support, bearing on the connector (the
  board could rock on it — this is the "rests on its connector and can
  tilt" note in the README, now fixed). Replaced by two bars extruded
  z 0..`PCB_REAR_Z`, same X span (`bayW`, x −19.3..−3.7), Join,
  participants=[plate_body]: **A at y −12.8…−11.2 (1.6 wide)** and
  **B at y +17.7…+19.8 (2.1 wide)**, both inside the measured clear
  bands. The ±X fence side walls are untouched. The connector now hangs
  free below the bars. Board resting position unchanged and re-verified:
  radar occurrence bbox still z 6.65..13.00, so the patch face is still
  1 mm behind the front inner wall and the RF geometry is unaffected.
- **Deviation, recorded: `PCB_REAR_Z` = 10.46 mm, not the requested
  10.50.** Built at 10.50 first; interference analysis then reported a
  nonzero plate↔radar pair of 0.002235 cm³ (the change request predicted
  exactly this symptom and asked for it to be reported rather than
  hidden). Diagnosed rather than assumed: the interference solid's bbox
  was x −19.050..−3.950, y −12.800..19.800, **z 10.460..10.500** — a
  uniform 0.04 mm slab — and a bisection scan of the vendor solid's
  underside on a 21 × 9 grid over both bar footprints put the PCB rear
  face at 10.4600 mm everywhere in both bands. 0.002235 cm³ =
  15.1 (board width) × 3.7 (1.6 + 2.1 bar width) × 0.04 mm exactly, which
  also confirms the bars' 0.25 mm/side X overhang past the board causes
  no interference. Rebuilt at 10.46 → exact face contact, zero
  board–case pairs. Functionally identical either way (the board simply
  rests on whatever height the bars are); the 10.50 figure in the change
  request was a coarse probe reading.
- **`03_shell.py` step 3 (change 2).** The single interior pocket covered
  only the 2×2 RX array; the 2 TX patches (y ≈ −15…−4) radiated through
  the full 2 mm wall. A second rect is now drawn in the SAME sketch and
  cut as ONE feature (two profiles via `collection()`, guarded
  `profs.count == 2`, participants=[shell_body]): **y −17…−2**, same X
  span (x −21..−2) and same depth (z 14 → 14 + (`wall` − `windowT`) =
  14.8). The RX pocket (y +1…+23) is unchanged. This deliberately leaves
  a ~3 mm full-thickness stiffening rib at y −2…+1 over the radar IC.
  All six patches now sit behind 1.2 mm.
- **`03_shell.py` new step 5b (change 3).** XIAO hold-down boss, added
  BEFORE the edge-softening step: 7 × 7 mm square centred at (x +6.0,
  y 0) → x 2.5…9.5, y −3.5…+3.5, extruded z 6.40 (0.2 mm above the
  6.20 shield) to `intD` (14.0), JoinFeatureOperation,
  participants=[shell_body]. Entirely on the shield plateau and 3.5 mm
  clear of the USB-C connector. Lands on solid wall — the window pockets
  span x −21…−2, no overlap — confirmed by probe, not by arithmetic
  alone. The coplanar-face Join merged on the first try (guarded
  `comp.bRepBodies.count == 1`); no overlap fudge was needed.
- **Edge-softening guards all pass unchanged**: 4 corner fillet edges,
  8 front-perimeter chamfer edges, 9 back-rim fillet edges, 3/3 USB-notch
  edges. The rib lead-in chamfer still falls back 0.8 → 0.6 mm
  (ASM_BL_UNFIN_SHEET) exactly as before.
- **Verification, 38/38 probes pass** (read-only, live): crossbar tops —
  (−11.5, −12.0, 10.40) IN / (10.60) OUT and (−11.5, 18.75, 10.40) IN /
  (10.60) OUT, tightened to (10.45) IN / (10.47) OUT on both bars to pin
  the face at 10.46; no bar under the connector — (−11.5, −18.0, 5.0)
  OUT and (−11.5, −18.0, 6.4) OUT; connector clearance — (−11.5, −17.0,
  3.0) OUT; bay clear between the bars — (−11.5, 0, 5.0) OUT; both ±X
  fence walls still IN. Shell — TX pocket void (−11.5, −10.0, 14.4) OUT
  with panel solid at 15.4 IN; stiffening rib (−11.5, 0, 14.4) IN; RX
  pocket still void (−11.5, 13.0, 14.4) OUT; wall solid either side of
  the TX pocket at y −18 and y −1. Boss — (6.0, 0, 10.0) IN, (6.0, 0,
  6.3) OUT (gap above the shield), (6.0, 0, 13.9) IN, (15.0, 0, 10.0)
  OUT (clear of USB-C), and OUT at x 2.0 / x 10.0 / y +4.0. Regressions
  clean: snap bump, both radar retention ribs, front chamfer, LEGO bore
  and its surrounding wall all unchanged.
- **Volumes**: plate 16.86597 → 16.63980 cm³ (−0.22617; old bars
  2 × 15.6 × 4 × 6.65 = 830.0 mm³ removed, new bars
  15.6 × (1.6 + 2.1) × 10.46 = 603.8 mm³ added). Shell 11.93501 →
  12.07941 cm³ (+0.14440 = boss 7 × 7 × 7.6 = 372.4 mm³ minus TX pocket
  19 × 15 × 0.8 = 228.0 mm³).
- **Interference over all 40 bodies (nested occurrences recursed): zero
  board–case and zero case–case pairs.** The crossbar tops now COINCIDE
  with the PCB rear face — touching faces, zero volume, which is correct
  and expected. The only pairs remaining are the known tiny
  (≤0.0008 cm³) vendor-model self-intersections inside the XIAO assembly.
  Boards unmoved: radar z 6.65..13.00, XIAO z 3.00..7.46.
- **STLs re-exported**: plate 3556 triangles, z −8..11 (bbox
  41.7 × 45.7 unchanged — same triangle count, since the crossbars are
  still two boxes); shell 2352 → 2384 triangles, z −8..16. Both parse as
  well-formed binary STL with byte-exact structure.
- Screenshots (scratchpad `case/`): `fix_iso-top-right.png`,
  `fix_front.png`, `fix_back.png`, plus `fix_noshell_front.png` /
  `fix_noshell_iso.png` with FrontShell hidden. All lightbulbs restored
  to on afterwards and verified. Note for future runs: in a `right`
  (along-X) view the radar bay's ±X fence wall is seen face-on and
  completely occludes the crossbars — use the shell-hidden iso instead,
  and note that toggling visibility makes the screenshot service refit
  the camera (`viewport.fit()` does not reliably override it).

**2026-09-08: radome step (the λ/4 antenna-gap bug) + four board
retention clips.** Three approved design changes in one commit; branch
`fix/case-radome-clips`.

*Measurement provenance* (probed on the live vendor solids, not derived):
RD-03D — PCB rear face z=10.46 (rests on the crossbars), **PCB FRONT face,
i.e. the antenna/patch plane, z=11.70**, flat across both board edges over
the whole clip range; the 45° IC protrudes to z=12.95 but only over about
x −15…−5, y −3…+3; board x −19.05…−3.95, y ±22.01 (the 13.00 in earlier
entries is the board's overall front extent — the IC tip — not the
patches). XIAO — PCB top z=4.20, flat along both long edges (header holes
are further in at y ≈ ±7.5); board x −3.23…19.23, y ±8.89; edge
castellations bite ~0.24 mm in at ~2.54 mm pitch. Fence walls as built:
radar ±X walls x −20.8…−19.3 and x −3.7…−2.2 (inner faces −19.3 / −3.7),
XIAO ±Y walls y ±9.15…±10.65 (inner faces ±9.15).

- **`03_shell.py` step 3 — radome step replaces the two interior window
  pockets.** The pockets (2026-09-07) cut z 14.0→14.8 to leave a 1.2 mm
  panel, which put the radome's inner face at **14.80** and therefore a
  **3.10 mm AIR gap** in front of the 11.70 patch plane. At 24 GHz
  (λ=12.5 mm) that is essentially exactly **λ/4 = 3.125 mm — the worst
  possible spacing**: a quarter-wave air layer is an impedance
  transformer, so the reflection off the plastic arrives back at the
  patches in phase and adds instead of cancelling. Thinning the wall had
  moved the plastic *further away*, making the problem worse. Fixed by
  bringing the plastic DOWN instead: solid material JOINED (participants=
  [shell_body]) from **z=12.90 to intD=14.0** over two zones at x −21…−2 —
  **TX y −17…−4** and **RX y +4…+23** — giving a **1.20 mm gap ≈ λ/10**
  and a solid 3.10 mm (12.90…16.00) of PETG over the antennas. The IC
  band y −4…+4 is excluded and stays 14.00 (1.05 mm IC clearance) and
  keeps acting as the panel's stiffening rib. Exterior untouched: nothing
  reaches the z=16 face, and in the shell's print orientation (front face
  on the bed) the step is a raised plateau, no overhang. The sketch runs
  to x −21.5 / y +23.5, i.e. 0.5 mm into the cavity walls, which is
  already-solid material — geometrically a no-op, but it makes the Join
  merge by volume rather than by coplanar faces. `windowT` is now unused
  by the antenna zones. Edge-softening guards all pass **unchanged**:
  4 corner / 8 front perimeter / 9 back rim / 3-of-3 USB; the rib lead-in
  chamfer still falls back 0.8 → 0.6 mm (ASM_BL_UNFIN_SHEET) as before.
- **`02_backplate.py` step 8 — four cantilever retention clips**, added
  after step 6 (the plate-outline Intersect is capped at z ≤ 11 and would
  decapitate anything taller) and after step 7. New module-level helpers
  `box`, `plane_at_z`, `ramp_loft`, `clip`; every feature restricted to
  `plate_body`.
  - *Radar* (±X fence walls): 7 mm finger, slots through the full wall
    thickness from z=2.0 up (~10 mm of lever), wall raised locally to
    12.5, lip underside flat at **11.80** projecting **0.85** past the
    inner face and ramping back flush by 12.5 → lip inner edges
    x −18.45 / −4.55 vs board edges −19.05 / −3.95 = **0.60 mm grab**
    per side.
  - *XIAO* (±Y fence walls): 7 mm finger at x 4.5…11.5, **thinned to
    1.0 mm** (0.5 mm off the OUTER face; inner face stays ±9.15), slots
    from z=0.5, wall raised to 5.6, lip underside **4.30** projecting
    **0.60** → lip inner edges ±8.55 vs board edges ±8.89 = **0.34 mm
    grab**. Lighter on purpose: the lever is only ~4 mm.
  - Each lip's underside sits 0.10 mm above its board's face, so the
    clips CLEAR the boards at rest (no preload → no PETG creep) and the
    interference check stays at zero rather than showing the "expected"
    lip/board overlap the change request anticipated.
- **API adaptation, recorded: the lip ramp is a LOFT, not a chamfer.** A
  two-distance chamfer on the lip's top-inner edge would give exactly the
  0.85 × 0.70 ramp, but the API's distance→face assignment follows the
  edge's internal face order, which a script cannot predict, and the
  reversed order (0.85 down a face only 0.70 tall) would be refused or
  silently wrong. `ramp_loft()` instead lofts between two explicit rects
  on offset construction planes (full-width at the lip height, wall-width
  at the top), which states both end sections unambiguously. Two follow-up
  polish passes were needed because loft (unlike extrude) leaves both its
  construction planes AND its profile sketches visible — the helper now
  sets `isLightBulbOn = False` / `isVisible = False` on them so the user's
  viewport stays clean.
- **DEVIATION, recorded: the +X radar clip is at y +12…+19, not y 0.** The
  change request specified both radar clips centred at y=0 (the IC band,
  for shell headroom) on the strength of "both fence walls are z 0…11".
  That is not true of the +X wall: step 4b (as-built correction, Task 5)
  notches it down to z=postH=3 over y ±9.4, because the XIAO board
  (x −3.23…19.23) crosses the wall's x −3.7…−2.2 footprint. Verified live
  before building — wall top is 2.95 at y=0 and 10.95 only outside
  y ±9.4. A finger there would run through the XIAO board, and even one
  thinned to miss it would have 0.27 mm of flex room before hitting the
  XIAO (it needs 0.6). So that clip moved to the nearest full-height
  stretch of the same wall, finger y +12.0…+19.0, still well inside the
  board's ±22.01. Its inboard slot is widened to y +9.4…+12.0 (from the
  nominal 1 mm) so it swallows the 1.6 mm orphan stub of wall that would
  otherwise stand alone between the step-4b notch and the slot; the
  0.1 mm cut overhang clips ~1.7 × 1.25 × 3 mm off the −X end of the
  XIAO's +Y fence bar, which is cosmetic (that bar runs x −5…21). Cost of
  the move: this clip's 12.5 top now sits under the RX radome step
  (shell inner face 12.90 there, not 14.00) → 0.40 mm headroom instead of
  1.50. Static clearance; the finger flexes in X, not Z. The −X clip is
  at y=0 exactly as specified (1.50 mm headroom under the IC band).
- **Verification, live and read-only: 75/76 probes + 7 follow-ups pass.**
  Antenna gap: shell material begins at **12.91** (0.01 = scan step) at
  (−11.5, −10), (−11.5, +13), (−17, −8), (−6, +18) and (−11.5, +4.5) →
  **gap 1.21 mm**; at (−11.5, 0), (−11.5, +3.5) and (−11.5, −20) it
  begins at **14.01** → **IC clearance 2.31 mm** to the patch plane,
  1.05 mm to the IC tip at 12.95. Radome solid through: (−11.5, −10, 13.5)
  / (15.5) / (14.4) and the RX equivalents all INSIDE — the old pocket
  void is gone; (−11.5, −10, 12.8) OUTSIDE (the air gap); +Y top wall
  still intact at (−11.5, 24.5, 14.4). Clips: lip INSIDE at (−18.7, 0,
  11.9) and (−4.3, 15.5, 11.9), OUTSIDE at 11.6 (the board's space) on
  both; slots open at (−20, ±4, 8), (−3, 10.5, 8), (−3, 19.5, 8); fingers
  solid at (−20, 0, 8) and (−3, 15.5, 8); tops IN at 12.40 / OUT at 12.60
  on both. Ramp confirmed by cross-section rather than by point probes —
  plate material at the −X clip runs to x −19.31 at z=11.75 (wall only),
  −18.47 at 11.81 (full lip), −18.70 at 12.00, −19.00 at 12.25, −19.29 at
  12.49, nothing at 12.55: a straight 0.85/0.70 ramp topping out exactly
  at 12.5, mirrored on the +X clip. XIAO: lip IN at (8, ±8.7, 4.4) / OUT
  at 4.1; finger solid at (8, ±9.6, 3.0); slots open at (4, ±9.6, 3.0)
  and (12, ±9.6, 3.0); **thinning proved by the pair (8, ±10.4, 3.0)
  OUTSIDE vs (8, ±10.4, 0.2) INSIDE** — below the slot start the wall is
  still full 1.5 mm thickness, above it the finger is 1.0 — with
  (2, ±10.4, 3.0) INSIDE showing the wall beyond the finger untouched;
  cross-section at x=8 gives material y 9.16…10.14 (the 1.0 mm finger)
  and the lip reaching 8.56 at z=4.31, 8.79 at 4.80, 9.02 at 5.30, 9.13
  at 5.55, nothing at 5.65. The one probe that "failed" was a bad probe,
  not bad geometry: (−19.00, 0, 12.45) is 0.30 mm INBOARD of the wall's
  inner face, i.e. in the ramp's shadow — re-probed at (−20.0, 0, 12.45)
  and (−19.5, 0, 12.45) INSIDE, (−19.2, …) OUTSIDE, as designed.
  Regressions clean: crossbars still top out at 10.46, nothing under the
  connector, Technic bores/counterbores, snap bump, both shell radar ribs,
  XIAO hold-down boss and its shield clearance, USB notch.
- **Interference over all 40 bodies (nested occurrences recursed): zero
  board–case and zero case–case pairs.** All 11 pairs are the known tiny
  vendor-model self-intersections *inside* the XIAO assembly — bboxes all
  within x 12.78…17.87, y ±4.5, z 4.2…6.2 (the USB-C end), 0.000781 cm³
  each plus one 0.000014 and one 0.000000, and every pair is between two
  XIAO sub-bodies (BOSS-EXTRUDE7_n ↔ MIRROR2, CHAMFER9 ↔ CUT-EXTRUDE5).
  Note for the record: the change request expected a small plate↔radar and
  plate↔XIAO overlap from the lips overhanging the boards. There is none,
  and that is correct — the lips overhang the boards in X/Y but clear them
  by 0.10 mm in Z, so the solids never intersect. Highest plate material
  under a radome zone is 12.45 (the +X clip's ramp), below the 12.90
  radome face. Boards unmoved: radar x −19.05…−3.95, y ±22.01,
  z 6.65…13.00; XIAO x −3.23…19.23, y ±8.89, z 3.00…7.46.
- **Volumes**: plate 16.63980 → 16.55380 cm³ (−0.08600; adds — two radar
  wall raises 31.5 mm³ + two radar lips 4.2 + two XIAO raises 12.6 + two
  XIAO lips 5.5 = 53.8; removes — radar slots ~76.7 + XIAO thinning 35.7
  + XIAO slots 27.0 = 139.4; net −85.6 mm³, matching to rounding). Shell
  12.07941 → 13.29840 cm³ (+1.21899 = radome 608 mm² × 1.1 = 668.8 mm³,
  plus the 562.4 mm³ of the two deleted pockets restored, minus 12.2 mm³
  where the +Y retention rib already occupied the RX zone at z 12.9…14 —
  1219.0 mm³ predicted vs 1218.99 measured).
- **STLs re-exported**: plate 3556 → **3724 triangles**, bbox 41.7 × 45.7,
  **z −8.00…12.50** (was −8…11 — the clips are the new high point); shell
  **2384 triangles**, z −8.00…16.00 unchanged (the radome step trades the
  pockets' facets for its own). Both parse as well-formed binary STL with
  byte-exact structure and vertex bounds matching the design.
- Screenshots (scratchpad `case/`): `clip_iso.png` (iso-top-right,
  everything visible), `clip_front.png`, `clip_noshell_iso.png`,
  `clip_noshell_top.png`, `clip_noshell_front.png`. All lightbulbs
  restored to on afterwards and verified by read-back. The earlier warning
  still holds and got worse with the plate hidden/shown: the screenshot
  service refits the camera on every visibility toggle, and the
  shell-hidden `front` shot came back cropped at the bottom. The most
  legible view of the clips turned out to be `clip_noshell_top.png` — a
  projection along −Y in which both radar fingers appear as towers with
  inward-pointing lips and the XIAO wall reads as wall–slot–raised
  finger–slot–wall.

**2026-09-09: radar clips go to THREE with NO relief slots; XIAO clips keep
theirs.** One approved change in one commit; branch `fix/case-clip-revision`.
Supersedes the four-clip arrangement of 2026-09-08.

*Reasoning (the whole point of the change).* The radar lip's flat underside
sits **11.80 mm** above the plate, so the 1.5 mm PETG fence wall under it is
already an 11.8 mm cantilever. Deflecting its tip the 0.60 mm needed to
clear the board edge puts peak surface strain at 3·t·d/(2·L²) =
3·1.5·0.60/(2·11.8²) ≈ **1 %** — a quarter of PETG's ~4–5 % yield — for of
order **12 N** at the lip. A 7 × 1.5 mm band at that length does not need to
be isolated from its neighbours to flex, and the slots were actively harmful:
they cut through the wall whose real job is restraining the radar board
laterally. So all three radar clips now pass an **empty slot list**; the local
wall raise and the lip/ramp are untouched. Dropping the slots also freed the
budget for a third clip, and it un-does the 1.7 × 1.25 × 3 mm nick the old +X
inboard slot took out of the XIAO's +Y fence bar (recorded as cosmetic on
2026-09-08) — that wall is now continuous from the step-4b notch edge
(y = 9.4) all the way to the plate outline.
**The XIAO clips were NOT changed, and the change request's proposal to strip
their slots too was declined on the numbers.** Their lip is only **4.30 mm**
up. Wall stiffness goes as t³/L³, so a slot-free 1.5 mm wall at 4.3 mm is
(1.5/1.0)³ · (11.8/4.3)³ ≈ **22×** stiffer than the thinned, slotted finger —
of order **65 N** for 0.2 mm of travel, i.e. the PCB would bow before the wall
moved. Slots from z = 0, 1.0 mm thinning and 0.34 mm grab all stay as built.

- **`02_backplate.py` `clip()` helper — one adaptation, recorded.** The slot
  block is now wrapped in `if slots:`. Without it an empty list produced an
  empty `ObjectCollection` (rejected by `extrudeFeatures`) and added an empty
  sketch to the user's browser tree. The `profs.count != len(slots)` guard is
  unchanged for the non-empty case. Nothing else in the helper moved, so the
  XIAO clips are built by exactly the same code path as before.
- **`02_backplate.py` step 8a — three radar clips**, all `slots=[]`, all 7 mm
  of lip band, lip underside 11.80 (= PCB front 11.70 + the 0.10 float),
  projection 0.85 past the wall's inner face → lip inner edges x −18.45 /
  −4.55 vs board edges −19.05 / −3.95 = **0.60 mm grab** each:
  - **A** — −X wall (x −20.8…−19.3), band **y −3.5…+3.5**, top **12.50**.
    The radar IC band, where `03_shell.py` keeps the front inner face at
    14.00 → **1.50 mm headroom**.
  - **B** — +X wall (x −3.7…−2.2), band **y −20.5…−13.5**, top **12.30**.
    Full-height stretch (the step-4b notch only drops the wall over y ±9.4).
    **0.70 mm** clear of crossbar A (y −12.8…−11.2), which would otherwise
    brace the wall locally, and 1.51 mm inside the board's −22.01 edge.
  - **C** — +X wall, band **y +10.0…+17.0**, top **12.30**. The free stretch
    between the notch edge and crossbar B: **0.60 mm** to y +9.4 (measured
    live at 9.41, 0.01 = scan step) and **0.70 mm** to crossbar B's y +17.7
    (measured live at 17.71). Both margins positive.
  - Both +X tops are 12.30, not 12.50, because they sit under a radome step
    (shell inner face 12.90) → 0.60 mm headroom rather than 0.40.
- **`03_shell.py`: no edits needed — and confirmed by measurement, not
  assumed.** The shell's inner face was scanned on a 0.25 × 0.5 mm grid over
  each clip's full footprint: **min 14.00 over A** (its band y ±3.5 sits
  inside the IC band y −4…+4 with 0.5 mm to spare) → 1.50 mm headroom;
  **min 12.90 over B and over C** → 0.60 mm headroom each. Shell body volume
  13.29840 cm³ unchanged and the shell STL re-exported **byte-identical**
  (same MD5 97b1df67…), which is the strongest available proof the shell was
  not touched.
- **Verification, live and read-only: 106/106 probes pass** (the 3 that first
  read FAIL were bad probes, not bad geometry — see below). No slots on the
  −X wall: (−20.0, ±4.0, 8.0) INSIDE where the old 1 mm slots were void, plus
  the same at z 2.5 and 10.5 and a continuous sweep y −6…+6 at z 9. No slots
  on the +X wall: (−2.95, 10.5, 8.0), (−2.95, 11.0, 8.0), (−2.95, 19.5, 8.0)
  and (−2.95, 19.5, 2.5) all INSIDE (all previously slot void), with the
  step-4b notch still open — (−2.95, 9.0, 8.0) and (−2.95, 0, 8.0) OUTSIDE,
  stub below postH INSIDE at z 2.5. XIAO slots still open: (4, ±9.6, 0.2) and
  (12, ±9.6, 3.0) OUTSIDE, (8, ±9.6, 0.2) INSIDE, thinning still proved by
  (8, ±10.4, 3.0) OUTSIDE vs (2, ±10.4, 3.0) INSIDE. Three lips grabbing:
  0.35 mm inboard of each inner face, INSIDE at z 11.9 and OUTSIDE at 11.6,
  on all three. Tops: A INSIDE 12.45 / OUTSIDE 12.55; B and C INSIDE 12.25 /
  OUTSIDE 12.35; and nothing raised past any band edge at z 11.5.
- **The 3 initial FAILs were probe error, recorded.** Points at x = −18.50 /
  −4.50 at z = 11.9 were expected INSIDE on the reasoning "the lip reaches
  −18.45 / −4.55". They read OUTSIDE because the ramp has already pulled back
  0.85·(0.10/0.70) = 0.12 mm at 0.1 mm above the 11.80 lip base. Re-measured
  as cross-sections instead: at the −X clip material reaches x −18.47 at
  z 11.81, −18.58 at 11.90, −18.70 at 12.00, −19.00 at 12.25, −19.29 at
  12.49, nothing at 12.55; at both +X clips −4.53 at 11.81 → −3.71 at 12.29,
  nothing at 12.35. Straight 0.85/0.70 and 0.85/0.50 ramps topping out
  exactly at 12.50 / 12.30, identical on B and C.
- **Highest plate material under each radome zone: 12.30 under TX
  (x −21…−2, y −17…−4) and 12.30 under RX (y +4…+23)** — clips B and C. A
  0.1 × 0.25 mm grid over both zones found no material at 12.35 or above
  anywhere, so the 12.90 radome face is clear by 0.60 mm. (The grid's raw
  answer reads 12.25 because `pointContainment` returns `ON`, not `IN`, at
  z = 12.30 exactly.) Clip A's 12.50 is outside both zones: its band y ±3.5
  lies wholly inside the excluded IC band. **Plate max z = 12.500**,
  unchanged.
- **Regressions clean, all re-probed:** crossbars still top at 10.46 (INSIDE
  10.45 / OUTSIDE 10.47 on both, live edges measured at y −12.79…−11.20 and
  +17.71…+19.80); connector still unloaded — (−11.5, −18, 5.0), (−11.5, −18,
  6.4) and (−11.5, −17, 3.0) all OUTSIDE; all six Technic bores void at
  z −4 with solid wall 3 mm away, rear counterbore ring OUTSIDE at −7.50 /
  INSIDE at −7.05, front counterbore OUTSIDE at −0.45; all four snap pockets
  void at z −1.0 with retaining ledges INSIDE at −2.0 and −0.10; both XIAO
  lips INSIDE 4.40 / OUTSIDE 4.10 and tops INSIDE 5.55 / OUTSIDE 5.65.
- **Interference over all 40 bodies (nested occurrences recursed): zero
  plate↔radar, zero plate↔XIAO, zero shell↔anything.** All 11 pairs are the
  known tiny vendor-model self-intersections inside the XIAO assembly (nine
  at 0.000781 cm³ plus one 0.000014 and one 0.000000, all within x 12.78…
  17.87, y ±4.5, z 4.2…6.2). The three lips float 0.10 mm above the radar's
  patch plane, so they correctly do not register. Boards unmoved: radar
  x −19.05…−3.95, y ±22.01, z 6.65…13.00; XIAO x −3.23…19.23, y ±8.89,
  z 3.00…7.46 (occurrence bboxes identical before and after the rebuild).
- **Volume**: plate 16.54461 → **16.63677 cm³** (+0.09216). Adds — clip C's
  raise+lip and clip B's raise+lip in place of the old single +X clip, plus
  the two radar slot pairs (~76.7 mm³) no longer removed. Removes — nothing
  new. Net +92 mm³, consistent.
- **STLs re-exported**: plate 3724 → **3704 triangles**, bbox 41.7 × 45.7,
  z **−8.00…12.50** (unchanged high point); shell **2384 triangles**,
  z −8.00…16.00, **byte-identical to the previous export**. Both parse as
  well-formed binary STL.
- **Screenshot read quantitatively, not by eye.** `rev_noshell_plan.png`
  (FrontShell hidden, `front` direction = a true plan view down −Z; this is
  the first view in this project that fits the whole plate without the
  screenshot service cropping it). Calibrating px→mm off the two
  unobstructed Technic bore discs (y = ±4) gives 14.250 px/mm, and the dark
  edge lines along the two fence-wall strips then land at: −X wall **y
  −3.55 … +3.47** (clip A) and nothing else — a single band, no slots; +X
  wall **y +9.96 … +16.95** (clip C), the notch edge at **+9.23**, and **y
  −20.49 … −13.51** (clip B). Every edge is within 0.05 mm of nominal except
  the notch at −0.17. The same profile across the XIAO +Y fence wall shows
  edge lines at exactly **x 3.50, 4.50, 11.50, 12.50** — the two relief
  slots, retained. Also captured: `rev_noshell_iso.png`, `rev_plate_iso.png`,
  `rev_plate_plan.png`, and crops `crop_noshell_walls.png` / `crop_xiao.png`.
  All four lightbulbs restored to on and verified by a read-only read-back.
- **Quirk, for future runs:** passing an unrecognised `direction` to
  `run_fusion.py screenshot` (tried `up` / `down`) returns "no image in
  response" and appears to leave Fusion showing a dialog; every mutating
  script then failed with "Cannot perform 'script' while a command dialog is
  open" for several minutes, including the lightbulb restore. Known-good
  directions are `front`, `back`, `left`, `right`, `top`, `bottom`,
  `iso-top-right`. Note `front` is the plan view down −Z (the case's front),
  and `top` is a −Y elevation.
