nThanksForAllTheFish/rd03d/docs/superpowers/plans/2026-08-31-rd03d-uart.md

# RD-03D UART Reader Implementation Plan

> **For agentic workers:** REQUIRED SUB-SKILL: Use superpowers:subagent-driven-development (recommended) or superpowers:executing-plans to implement this plan task-by-task. Steps use checkbox (`- [ ]`) syntax for tracking.

**Goal:** XIAO ESP32-C6 reads 30-byte binary frames from an RD-03D radar on UART1 (256000 baud), decodes up to 3 targets, and prints one human-readable line per frame to the USB-C serial console.

**Architecture:** Single FreeRTOS task polls `uart_read_bytes()` and feeds bytes into a pure-C parser state machine (`rd03d.c`) that resynchronizes on the `AA FF 03 00` header and validates the `55 CC` tail. The parser has no ESP-IDF dependencies, so it is unit-tested on the host with plain `cc` before ever touching hardware.

**Tech Stack:** ESP-IDF **v5.5** (`~/esp/esp-idf-v5.5` — note: the spec says v5.3.5, but that install was removed from this machine; v5.5 is the known-good install), FreeRTOS, UART driver, USB-Serial-JTAG console.

**Spec:** `docs/superpowers/specs/2026-08-31-rd03d-uart-design.md`

**Environment setup (needed in every build shell):**

```bash
source ~/esp/esp-idf-v5.5/export.sh
```

Serial port for flashing/monitor: `/dev/cu.usbmodem101` (may enumerate with a different number; check `ls /dev/cu.usbmodem*`).

**Frame format reference** (from `RD03D_RadarChart/RD03D_RadarChart.pde`):
30 bytes = header `AA FF 03 00` + 3 × 8-byte target blocks + tail `55 CC`.
Target block: X(2) Y(2) velocity(2) resolution(2), all little-endian.
X/Y (mm) and velocity (cm/s) use **sign-magnitude**: high byte MSB **set = positive**, **clear = negative**; magnitude = `((hi & 0x7F) << 8) | lo`. Resolution is plain unsigned LE. A target with x==0 and y==0 is "not present."

---

### Task 1: Scaffold the ESP-IDF project

**Files:**
- Create: `rd03d_uart/CMakeLists.txt`
- Create: `rd03d_uart/sdkconfig.defaults`
- Create: `rd03d_uart/main/CMakeLists.txt`
- Create: `rd03d_uart/main/main.c` (stub)

- [x] **Step 1: Create project CMakeLists**

`rd03d_uart/CMakeLists.txt`:

```cmake
# The following lines of boilerplate have to be in your project's
# CMakeLists in this exact order for cmake to work correctly
cmake_minimum_required(VERSION 3.16)

include($ENV{IDF_PATH}/tools/cmake/project.cmake)
project(rd03d_uart)
```

- [x] **Step 2: Create sdkconfig.defaults**

`rd03d_uart/sdkconfig.defaults`:

```
CONFIG_ESP_CONSOLE_USB_SERIAL_JTAG=y
```

- [x] **Step 3: Create main component CMakeLists**

`rd03d_uart/main/CMakeLists.txt`:

```cmake
idf_component_register(SRCS "main.c" "rd03d.c"
                    INCLUDE_DIRS "")
```

Note: `rd03d.c` doesn't exist until Task 2. To keep Task 1's build green, list only `"main.c"` here now and add `"rd03d.c"` in Task 2, OR create both files in this task with `rd03d.c` empty. **Do the former:** register only `"main.c"` now.

- [x] **Step 4: Create stub main.c**

`rd03d_uart/main/main.c`:

```c
#include <stdio.h>

void app_main(void)
{
    printf("rd03d_uart: stub\n");
}
```

- [x] **Step 5: Build to verify the scaffold**

```bash
source ~/esp/esp-idf-v5.5/export.sh
cd rd03d_uart
idf.py set-target esp32c6
idf.py build
```

Expected: `Project build complete.` with a `rd03d_uart.bin` artifact.

- [x] **Step 6: Commit**

```bash
git add rd03d_uart/CMakeLists.txt rd03d_uart/sdkconfig.defaults rd03d_uart/main/
git commit -m "feat(rd03d_uart): scaffold esp32c6 project"
```

Do NOT commit `rd03d_uart/build/` or `rd03d_uart/sdkconfig` (generated).

---

### Task 2: Sign-magnitude decoder (TDD, host-side)

**Files:**
- Create: `rd03d_uart/main/rd03d.h`
- Create: `rd03d_uart/main/rd03d.c`
- Create: `rd03d_uart/tests/test_rd03d.c`
- Modify: `rd03d_uart/main/CMakeLists.txt` (add `rd03d.c`)

- [x] **Step 1: Write the header (API contract)**

`rd03d_uart/main/rd03d.h`:

```c
#pragma once

#include <stdbool.h>
#include <stddef.h>
#include <stdint.h>

#define RD03D_NUM_TARGETS 3
#define RD03D_FRAME_LEN   30

typedef struct {
    bool present;            /* false when x==0 && y==0 */
    int16_t x_mm;
    int16_t y_mm;
    int16_t speed_cms;
    uint16_t resolution_mm;
} rd03d_target_t;

typedef struct {
    rd03d_target_t targets[RD03D_NUM_TARGETS];
} rd03d_frame_t;

typedef struct {
    uint8_t buf[RD03D_FRAME_LEN];
    size_t pos;
    uint32_t dropped_bytes;  /* bytes discarded while hunting for a header */
    uint32_t bad_frames;     /* frames with a corrupt tail */
} rd03d_parser_t;

/* RD-03D sign-magnitude: high-byte MSB set = positive, clear = negative. */
int16_t rd03d_decode_sign_mag(uint8_t lo, uint8_t hi);

void rd03d_parser_init(rd03d_parser_t *p);

/* Feed one byte. Returns true when a complete valid frame was written to *frame. */
bool rd03d_parser_feed(rd03d_parser_t *p, uint8_t byte, rd03d_frame_t *frame);
```

- [x] **Step 2: Write the failing decode test**

`rd03d_uart/tests/test_rd03d.c`:

```c
#include <assert.h>
#include <stdio.h>
#include "../main/rd03d.h"

static void test_decode_sign_mag(void)
{
    /* MSB of high byte set -> positive: 0x8102 -> +0x0102 = +258 */
    assert(rd03d_decode_sign_mag(0x02, 0x81) == 258);
    /* MSB clear -> negative: 0x03E8 -> -1000 */
    assert(rd03d_decode_sign_mag(0xE8, 0x03) == -1000);
    /* Positive small value: 0x8019 -> +25 */
    assert(rd03d_decode_sign_mag(0x19, 0x80) == 25);
    /* Zero stays zero */
    assert(rd03d_decode_sign_mag(0x00, 0x00) == 0);
}

int main(void)
{
    test_decode_sign_mag();
    printf("all tests passed\n");
    return 0;
}
```

- [x] **Step 3: Run the test to verify it fails**

```bash
cd rd03d_uart/tests
cc -Wall -Wextra -o test_rd03d test_rd03d.c ../main/rd03d.c && ./test_rd03d
```

Expected: compile FAILURE — `../main/rd03d.c: No such file or directory` (or undefined symbol `rd03d_decode_sign_mag`).

- [x] **Step 4: Write the minimal implementation**

`rd03d_uart/main/rd03d.c`:

```c
#include "rd03d.h"

int16_t rd03d_decode_sign_mag(uint8_t lo, uint8_t hi)
{
    int16_t magnitude = (int16_t)(((hi & 0x7F) << 8) | lo);
    return (hi & 0x80) ? magnitude : (int16_t)-magnitude;
}
```

- [x] **Step 5: Run the test to verify it passes**

```bash
cd rd03d_uart/tests
cc -Wall -Wextra -o test_rd03d test_rd03d.c ../main/rd03d.c && ./test_rd03d
```

Expected: `all tests passed`

- [x] **Step 6: Add rd03d.c to the firmware build**

Edit `rd03d_uart/main/CMakeLists.txt` to:

```cmake
idf_component_register(SRCS "main.c" "rd03d.c"
                    INCLUDE_DIRS "")
```

- [x] **Step 7: Commit**

```bash
git add rd03d_uart/main/rd03d.h rd03d_uart/main/rd03d.c rd03d_uart/tests/test_rd03d.c rd03d_uart/main/CMakeLists.txt
git commit -m "feat(rd03d_uart): add sign-magnitude decoder with host tests"
```

Do NOT commit the compiled `rd03d_uart/tests/test_rd03d` binary.

---

### Task 3: Frame parser state machine (TDD, host-side)

**Files:**
- Modify: `rd03d_uart/main/rd03d.c`
- Test: `rd03d_uart/tests/test_rd03d.c`

- [x] **Step 1: Add failing parser tests**

Add to `rd03d_uart/tests/test_rd03d.c` (above `main`), and call the three new
test functions from `main` before the `printf`:

```c
/* One valid frame: T1 at x=+258mm y=-1000mm v=+25cm/s res=360mm; T2/T3 absent. */
static const uint8_t GOOD_FRAME[RD03D_FRAME_LEN] = {
    0xAA, 0xFF, 0x03, 0x00,
    /* T1 */ 0x02, 0x81, 0xE8, 0x03, 0x19, 0x80, 0x68, 0x01,
    /* T2 */ 0x00, 0x00, 0x00, 0x00, 0x00, 0x00, 0x00, 0x00,
    /* T3 */ 0x00, 0x00, 0x00, 0x00, 0x00, 0x00, 0x00, 0x00,
    0x55, 0xCC,
};

static int feed_all(rd03d_parser_t *p, const uint8_t *bytes, size_t n,
                    rd03d_frame_t *frame)
{
    int frames = 0;
    for (size_t i = 0; i < n; i++) {
        if (rd03d_parser_feed(p, bytes[i], frame)) {
            frames++;
        }
    }
    return frames;
}

static void test_parse_good_frame(void)
{
    rd03d_parser_t p;
    rd03d_frame_t f;
    rd03d_parser_init(&p);

    assert(feed_all(&p, GOOD_FRAME, sizeof(GOOD_FRAME), &f) == 1);
    assert(f.targets[0].present);
    assert(f.targets[0].x_mm == 258);
    assert(f.targets[0].y_mm == -1000);
    assert(f.targets[0].speed_cms == 25);
    assert(f.targets[0].resolution_mm == 360);
    assert(!f.targets[1].present);
    assert(!f.targets[2].present);
    assert(p.dropped_bytes == 0);
    assert(p.bad_frames == 0);
}

static void test_resync_after_garbage(void)
{
    rd03d_parser_t p;
    rd03d_frame_t f;
    rd03d_parser_init(&p);

    /* Garbage prefix, including a lone 0xAA that is NOT a real header start. */
    const uint8_t garbage[] = {0x12, 0xAA, 0x34, 0x55, 0xCC};
    assert(feed_all(&p, garbage, sizeof(garbage), &f) == 0);
    assert(feed_all(&p, GOOD_FRAME, sizeof(GOOD_FRAME), &f) == 1);
    assert(f.targets[0].x_mm == 258);
    assert(p.dropped_bytes > 0);
}

static void test_bad_tail_counted_then_recovers(void)
{
    rd03d_parser_t p;
    rd03d_frame_t f;
    rd03d_parser_init(&p);

    uint8_t bad[RD03D_FRAME_LEN];
    for (size_t i = 0; i < RD03D_FRAME_LEN; i++) bad[i] = GOOD_FRAME[i];
    bad[29] = 0x00; /* corrupt tail */

    assert(feed_all(&p, bad, sizeof(bad), &f) == 0);
    assert(p.bad_frames == 1);
    /* Parser recovers: next clean frame parses. */
    assert(feed_all(&p, GOOD_FRAME, sizeof(GOOD_FRAME), &f) == 1);
}
```

- [x] **Step 2: Run the tests to verify they fail**

```bash
cd rd03d_uart/tests
cc -Wall -Wextra -o test_rd03d test_rd03d.c ../main/rd03d.c && ./test_rd03d
```

Expected: link FAILURE — undefined symbols `rd03d_parser_init` / `rd03d_parser_feed`.

- [x] **Step 3: Implement the parser**

Add to `rd03d_uart/main/rd03d.c`:

```c
#include <string.h>

static const uint8_t RD03D_HEADER[4] = {0xAA, 0xFF, 0x03, 0x00};

void rd03d_parser_init(rd03d_parser_t *p)
{
    memset(p, 0, sizeof(*p));
}

bool rd03d_parser_feed(rd03d_parser_t *p, uint8_t byte, rd03d_frame_t *frame)
{
    if (p->pos < sizeof(RD03D_HEADER)) {
        /* Hunting for / matching the header. */
        if (byte == RD03D_HEADER[p->pos]) {
            p->buf[p->pos++] = byte;
        } else {
            p->dropped_bytes += (uint32_t)p->pos + 1;
            /* The mismatched byte itself may start a new header. */
            if (byte == RD03D_HEADER[0]) {
                p->buf[0] = byte;
                p->pos = 1;
                p->dropped_bytes--; /* it wasn't dropped after all */
            } else {
                p->pos = 0;
            }
        }
        return false;
    }

    p->buf[p->pos++] = byte;
    if (p->pos < RD03D_FRAME_LEN) {
        return false;
    }
    p->pos = 0;

    if (p->buf[28] != 0x55 || p->buf[29] != 0xCC) {
        p->bad_frames++;
        return false;
    }

    for (int i = 0; i < RD03D_NUM_TARGETS; i++) {
        const uint8_t *b = &p->buf[4 + 8 * i];
        rd03d_target_t *t = &frame->targets[i];
        t->x_mm = rd03d_decode_sign_mag(b[0], b[1]);
        t->y_mm = rd03d_decode_sign_mag(b[2], b[3]);
        t->speed_cms = rd03d_decode_sign_mag(b[4], b[5]);
        t->resolution_mm = (uint16_t)(b[6] | (b[7] << 8));
        t->present = (t->x_mm != 0 || t->y_mm != 0);
    }
    return true;
}
```

- [x] **Step 4: Run the tests to verify they pass**

```bash
cd rd03d_uart/tests
cc -Wall -Wextra -o test_rd03d test_rd03d.c ../main/rd03d.c && ./test_rd03d
```

Expected: `all tests passed`

- [x] **Step 5: Commit**

```bash
git add rd03d_uart/main/rd03d.c rd03d_uart/tests/test_rd03d.c
git commit -m "feat(rd03d_uart): add frame parser with resync and host tests"
```

---

### Task 4: UART read task and console output

**Files:**
- Modify: `rd03d_uart/main/main.c` (replace stub entirely)

- [x] **Step 1: Write main.c**

Replace `rd03d_uart/main/main.c` with:

```c
#include <inttypes.h>
#include <stdio.h>

#include "freertos/FreeRTOS.h"
#include "freertos/task.h"
#include "driver/uart.h"
#include "esp_log.h"

#include "rd03d.h"

/* XIAO ESP32-C6: D6 = GPIO16 (UART1 TX), D7 = GPIO17 (UART1 RX). */
#define RADAR_UART_NUM   UART_NUM_1
#define RADAR_PIN_TX     16
#define RADAR_PIN_RX     17
#define RADAR_BAUD       256000
#define UART_RX_BUF_SIZE 1024
#define STATS_PERIOD_MS  5000

static const char *TAG = "rd03d";

static void print_frame(const rd03d_frame_t *f)
{
    char line[128];
    size_t off = 0;
    for (int i = 0; i < RD03D_NUM_TARGETS; i++) {
        const rd03d_target_t *t = &f->targets[i];
        const char *sep = (i < RD03D_NUM_TARGETS - 1) ? " | " : "";
        int n;
        if (t->present) {
            n = snprintf(line + off, sizeof(line) - off,
                         "T%d: x=%dmm y=%dmm v=%dcm/s%s",
                         i + 1, t->x_mm, t->y_mm, t->speed_cms, sep);
        } else {
            n = snprintf(line + off, sizeof(line) - off, "T%d: ---%s",
                         i + 1, sep);
        }
        if (n < 0 || (size_t)n >= sizeof(line) - off) {
            break;
        }
        off += (size_t)n;
    }
    printf("%s\n", line);
}

void app_main(void)
{
    const uart_config_t cfg = {
        .baud_rate = RADAR_BAUD,
        .data_bits = UART_DATA_8_BITS,
        .parity = UART_PARITY_DISABLE,
        .stop_bits = UART_STOP_BITS_1,
        .flow_ctrl = UART_HW_FLOWCTRL_DISABLE,
        .source_clk = UART_SCLK_DEFAULT,
    };
    ESP_ERROR_CHECK(uart_driver_install(RADAR_UART_NUM, UART_RX_BUF_SIZE,
                                        0, 0, NULL, 0));
    ESP_ERROR_CHECK(uart_param_config(RADAR_UART_NUM, &cfg));
    ESP_ERROR_CHECK(uart_set_pin(RADAR_UART_NUM, RADAR_PIN_TX, RADAR_PIN_RX,
                                 UART_PIN_NO_CHANGE, UART_PIN_NO_CHANGE));

    ESP_LOGI(TAG, "RD-03D reader: UART%d RX=GPIO%d TX=GPIO%d @ %d baud",
             RADAR_UART_NUM, RADAR_PIN_RX, RADAR_PIN_TX, RADAR_BAUD);

    rd03d_parser_t parser;
    rd03d_parser_init(&parser);
    rd03d_frame_t frame;
    uint8_t buf[128];
    TickType_t last_stats = xTaskGetTickCount();

    for (;;) {
        int n = uart_read_bytes(RADAR_UART_NUM, buf, sizeof(buf),
                                pdMS_TO_TICKS(100));
        for (int i = 0; i < n; i++) {
            if (rd03d_parser_feed(&parser, buf[i], &frame)) {
                print_frame(&frame);
            }
        }
        if (xTaskGetTickCount() - last_stats >= pdMS_TO_TICKS(STATS_PERIOD_MS)) {
            ESP_LOGI(TAG, "link stats: dropped=%" PRIu32 " bad_frames=%" PRIu32,
                     parser.dropped_bytes, parser.bad_frames);
            last_stats = xTaskGetTickCount();
        }
    }
}
```

- [x] **Step 2: Build**

```bash
source ~/esp/esp-idf-v5.5/export.sh
cd rd03d_uart
idf.py build
```

Expected: `Project build complete.` — no warnings from `main.c` or `rd03d.c`.

- [x] **Step 3: Re-run host tests (regression check)**

```bash
cd rd03d_uart/tests
cc -Wall -Wextra -o test_rd03d test_rd03d.c ../main/rd03d.c && ./test_rd03d
```

Expected: `all tests passed`

- [x] **Step 4: Commit**

```bash
git add rd03d_uart/main/main.c
git commit -m "feat(rd03d_uart): read radar frames on UART1 and print targets"
```

---

### Task 5: Flash, verify on hardware, and document

**Files:**
- Create: `rd03d_uart/README.md`

Hardware precondition — wire the RD-03D to the XIAO ESP32-C6:

| RD-03D | XIAO ESP32-C6 |
| --- | --- |
| TX | D7 (GPIO17) |
| RX | D6 (GPIO16) |
| 5V | 5V |
| GND | GND |

- [x] **Step 1: Flash and monitor**

```bash
source ~/esp/esp-idf-v5.5/export.sh
cd rd03d_uart
idf.py -p /dev/cu.usbmodem101 flash monitor
```

Expected: boot log ending with
`I (…) rd03d: RD-03D reader: UART1 RX=GPIO17 TX=GPIO16 @ 256000 baud`.
(If the port differs, find it with `ls /dev/cu.usbmodem*`. Exit monitor with Ctrl+].)

- [x] **Step 2: Verify radar data**

Move a hand or walk in front of the radar. Expected: continuous lines like

```
T1: x=-123mm y=456mm v=-12cm/s | T2: --- | T3: ---
```

with x/y changing as the target moves, and a stats line every ~5 s:
`I (…) rd03d: link stats: dropped=0 bad_frames=0`.
With no motion and no target, expect `T1: --- | T2: --- | T3: ---` or no frame lines (the RD-03D keeps streaming frames either way; both are acceptable).
If nothing arrives at all and `dropped` stays 0, the RX wire or baud is wrong — recheck that radar **TX** goes to **D7**.

- [x] **Step 3: Write README**

`rd03d_uart/README.md`:

```markdown
# rd03d_uart

XIAO ESP32-C6 firmware that reads an Ai-Thinker RD-03D 24GHz mmWave radar over
UART1 and prints decoded targets to the USB-C serial console.

## Wiring

| RD-03D | XIAO ESP32-C6 |
| --- | --- |
| TX | D7 (GPIO17) |
| RX | D6 (GPIO16) |
| 5V | 5V |
| GND | GND |

Radar UART: 256000 baud, 8N1.

## Build & flash

```bash
source ~/esp/esp-idf-v5.5/export.sh
idf.py set-target esp32c6   # first time only
idf.py -p /dev/cu.usbmodem101 flash monitor
```

## Output

One line per radar frame (up to 3 targets), plus link stats every 5 s:

```
T1: x=-123mm y=456mm v=-12cm/s | T2: --- | T3: ---
I (5210) rd03d: link stats: dropped=0 bad_frames=0
```

## Host-side parser tests

```bash
cd tests
cc -Wall -Wextra -o test_rd03d test_rd03d.c ../main/rd03d.c && ./test_rd03d
```

Frame format and sign-magnitude decoding match
`../RD03D_RadarChart/README.md` (Processing visualizer for the same sensor).
```

- [x] **Step 4: Commit**

```bash
git add rd03d_uart/README.md
git commit -m "docs(rd03d_uart): add wiring, build, and usage README"
```
