nThanksForAllTheFish/rd03d/docs/superpowers/plans/2026-09-06-rd03d-mqtt.md

# RD-03D MQTT Publishing Implementation Plan

> **For agentic workers:** REQUIRED SUB-SKILL: Use superpowers:subagent-driven-development (recommended) or superpowers:executing-plans to implement this plan task-by-task. Steps use checkbox (`- [ ]`) syntax for tracking.

**Goal:** The XIAO publishes per-target radar coordinates to MQTT broker `iotstack.local:1883` (topics `rd03d/target/1..3`, availability on `rd03d/status`), sending a new message only when a target moved ≥ a configurable distance (default 200 mm) — plus one `{"gone":true}` when a target disappears.

**Architecture:** Pure host-testable throttle core (`mqtt_throttle.c` — per-target published-position state machine) + thin esp-mqtt glue (`mqtt_pub.c` — resolves `.local` broker via the already-running mDNS stack, LWT on `rd03d/status`, resets throttle state on every CONNECTED so consumers get current state). `main.c` feeds every parsed frame to `mqtt_pub_frame`, which no-ops when disconnected. Feature delivered via OTA.

**Tech Stack:** ESP-IDF v5.5 built-in `mqtt` (esp-mqtt) component, `mdns_query_a`, Kconfig options (non-secret, committed defaults), host tests with plain `cc`, Mac-side verification with `paho-mqtt` in the scratchpad venv.

**Spec:** `docs/superpowers/specs/2026-09-06-rd03d-mqtt-design.md`

**Environment (every build shell):** `source ~/esp/esp-idf-v5.5/export.sh` combined with idf.py on one line (fresh shell per Bash call). Device: `rd03d.local` / 192.168.1.186, running from an OTA slot with rollback armed — deliver builds via `curl -X POST --data-binary @build/rd03d_uart.bin http://192.168.1.186/update` (~20 s to return; device validates itself). Board is also on USB at `/dev/cu.usbmodem11101` for console observation only — do NOT `idf.py flash`. `main/rd03d.c/.h` must not change. WiFi credentials live only in the untracked `sdkconfig` — never commit/echo; the new MQTT Kconfig symbols get their defaults automatically on the next build (no manual sdkconfig edits needed).

**Version-stamp discipline (learned in the OTA plan):** commit BEFORE building any image that will be delivered, and if unrelated files (e.g. this plan's checkboxes) are dirty at build time, `git stash push` them around the build so the stamp isn't `-dirty`.

---

### Task 1: Throttle core (TDD, host-side)

**Files:**
- Create: `rd03d_uart/main/mqtt_throttle.h`
- Create: `rd03d_uart/main/mqtt_throttle.c`
- Create: `rd03d_uart/tests/test_mqtt_throttle.c`
- Modify: `rd03d_uart/main/CMakeLists.txt`
- Modify: `.gitignore`

- [x] **Step 1: Write the header (API contract)**

`rd03d_uart/main/mqtt_throttle.h`:

```c
#pragma once

#include <stdbool.h>
#include <stdint.h>

#include "rd03d.h"

typedef enum {
    MQTT_THROTTLE_NONE = 0, /* nothing to publish for this target */
    MQTT_THROTTLE_MOVED,    /* publish coordinates */
    MQTT_THROTTLE_GONE,     /* publish the gone event */
} mqtt_throttle_action_t;

typedef struct {
    bool published;         /* a position has been published since reset */
    int16_t x_mm;           /* last PUBLISHED position (anchor for distance) */
    int16_t y_mm;
} mqtt_throttle_slot_t;

typedef struct {
    mqtt_throttle_slot_t slots[RD03D_NUM_TARGETS];
    uint32_t threshold_mm;
} mqtt_throttle_t;

void mqtt_throttle_init(mqtt_throttle_t *t, uint32_t threshold_mm);

/* Clear published state (call on MQTT reconnect) so present targets
 * republish immediately. Keeps the threshold. */
void mqtt_throttle_reset(mqtt_throttle_t *t);

/* Decide what to publish for target slot i (0-based) given its state in the
 * newest frame. Updates internal state when returning MOVED or GONE. Only
 * call while the MQTT connection is up — state must not advance while
 * publishes would be dropped. */
mqtt_throttle_action_t mqtt_throttle_eval(mqtt_throttle_t *t, int i,
                                          const rd03d_target_t *target);
```

- [x] **Step 2: Write the failing tests**

`rd03d_uart/tests/test_mqtt_throttle.c`:

```c
#include <assert.h>
#include <stdio.h>
#include "../main/mqtt_throttle.h"

static rd03d_target_t at(int16_t x, int16_t y)
{
    rd03d_target_t t = { .present = true, .x_mm = x, .y_mm = y,
                         .speed_cms = 0, .resolution_mm = 360 };
    return t;
}

static rd03d_target_t absent(void)
{
    rd03d_target_t t = { 0 };
    return t;
}

static void test_first_appearance_publishes(void)
{
    mqtt_throttle_t th;
    mqtt_throttle_init(&th, 200);
    rd03d_target_t t = at(100, 500);
    assert(mqtt_throttle_eval(&th, 0, &t) == MQTT_THROTTLE_MOVED);
}

static void test_small_move_is_silent(void)
{
    mqtt_throttle_t th;
    mqtt_throttle_init(&th, 200);
    rd03d_target_t t = at(100, 500);
    mqtt_throttle_eval(&th, 0, &t);
    t = at(199, 500); /* 99 mm from published anchor */
    assert(mqtt_throttle_eval(&th, 0, &t) == MQTT_THROTTLE_NONE);
    t = at(100, 640); /* 140 mm */
    assert(mqtt_throttle_eval(&th, 0, &t) == MQTT_THROTTLE_NONE);
}

static void test_drift_accumulates_from_anchor(void)
{
    /* Two sub-threshold steps in the same direction cross the threshold
     * relative to the PUBLISHED anchor, so the second one publishes. */
    mqtt_throttle_t th;
    mqtt_throttle_init(&th, 200);
    rd03d_target_t t = at(0, 500);
    mqtt_throttle_eval(&th, 0, &t);
    t = at(150, 500);
    assert(mqtt_throttle_eval(&th, 0, &t) == MQTT_THROTTLE_NONE);
    t = at(300, 500); /* 300 mm from anchor */
    assert(mqtt_throttle_eval(&th, 0, &t) == MQTT_THROTTLE_MOVED);
}

static void test_exact_threshold_publishes(void)
{
    mqtt_throttle_t th;
    mqtt_throttle_init(&th, 200);
    rd03d_target_t t = at(0, 500);
    mqtt_throttle_eval(&th, 0, &t);
    t = at(200, 500); /* exactly 200 mm */
    assert(mqtt_throttle_eval(&th, 0, &t) == MQTT_THROTTLE_MOVED);
}

static void test_moved_updates_anchor(void)
{
    mqtt_throttle_t th;
    mqtt_throttle_init(&th, 200);
    rd03d_target_t t = at(0, 500);
    mqtt_throttle_eval(&th, 0, &t);
    t = at(300, 500);
    mqtt_throttle_eval(&th, 0, &t); /* anchor now (300,500) */
    t = at(400, 500); /* 100 mm from new anchor */
    assert(mqtt_throttle_eval(&th, 0, &t) == MQTT_THROTTLE_NONE);
}

static void test_gone_fires_once(void)
{
    mqtt_throttle_t th;
    mqtt_throttle_init(&th, 200);
    rd03d_target_t t = at(100, 500);
    mqtt_throttle_eval(&th, 0, &t);
    rd03d_target_t a = absent();
    assert(mqtt_throttle_eval(&th, 0, &a) == MQTT_THROTTLE_GONE);
    assert(mqtt_throttle_eval(&th, 0, &a) == MQTT_THROTTLE_NONE);
}

static void test_absent_without_publish_is_silent(void)
{
    mqtt_throttle_t th;
    mqtt_throttle_init(&th, 200);
    rd03d_target_t a = absent();
    assert(mqtt_throttle_eval(&th, 0, &a) == MQTT_THROTTLE_NONE);
}

static void test_reset_republishes_present_target(void)
{
    mqtt_throttle_t th;
    mqtt_throttle_init(&th, 200);
    rd03d_target_t t = at(100, 500);
    mqtt_throttle_eval(&th, 0, &t);
    mqtt_throttle_reset(&th);
    assert(mqtt_throttle_eval(&th, 0, &t) == MQTT_THROTTLE_MOVED);
}

static void test_slots_are_independent(void)
{
    mqtt_throttle_t th;
    mqtt_throttle_init(&th, 200);
    rd03d_target_t t0 = at(100, 500);
    rd03d_target_t t1 = at(-900, 2000);
    assert(mqtt_throttle_eval(&th, 0, &t0) == MQTT_THROTTLE_MOVED);
    assert(mqtt_throttle_eval(&th, 1, &t1) == MQTT_THROTTLE_MOVED);
    t0 = at(100, 500);
    assert(mqtt_throttle_eval(&th, 0, &t0) == MQTT_THROTTLE_NONE);
    rd03d_target_t a = absent();
    assert(mqtt_throttle_eval(&th, 1, &a) == MQTT_THROTTLE_GONE);
}

static void test_extreme_coordinates_no_overflow(void)
{
    /* Corner-to-corner jump: dx=dy=65534 -> dx^2+dy^2 needs 64-bit math. */
    mqtt_throttle_t th;
    mqtt_throttle_init(&th, 200);
    rd03d_target_t t = at(-32767, -32767);
    mqtt_throttle_eval(&th, 0, &t);
    t = at(32767, 32767);
    assert(mqtt_throttle_eval(&th, 0, &t) == MQTT_THROTTLE_MOVED);
}

int main(void)
{
    test_first_appearance_publishes();
    test_small_move_is_silent();
    test_drift_accumulates_from_anchor();
    test_exact_threshold_publishes();
    test_moved_updates_anchor();
    test_gone_fires_once();
    test_absent_without_publish_is_silent();
    test_reset_republishes_present_target();
    test_slots_are_independent();
    test_extreme_coordinates_no_overflow();
    printf("all tests passed\n");
    return 0;
}
```

- [x] **Step 3: Run the tests to verify they fail**

```bash
cd rd03d_uart/tests && cc -Wall -Wextra -o test_mqtt_throttle test_mqtt_throttle.c ../main/mqtt_throttle.c && ./test_mqtt_throttle
```

Expected: compile FAILURE — `../main/mqtt_throttle.c: No such file or directory`.

- [x] **Step 4: Implement**

`rd03d_uart/main/mqtt_throttle.c`:

```c
#include "mqtt_throttle.h"

#include <string.h>

void mqtt_throttle_init(mqtt_throttle_t *t, uint32_t threshold_mm)
{
    memset(t, 0, sizeof(*t));
    t->threshold_mm = threshold_mm;
}

void mqtt_throttle_reset(mqtt_throttle_t *t)
{
    for (int i = 0; i < RD03D_NUM_TARGETS; i++) {
        t->slots[i].published = false;
    }
}

mqtt_throttle_action_t mqtt_throttle_eval(mqtt_throttle_t *t, int i,
                                          const rd03d_target_t *target)
{
    mqtt_throttle_slot_t *s = &t->slots[i];

    if (!target->present) {
        if (s->published) {
            s->published = false;
            return MQTT_THROTTLE_GONE;
        }
        return MQTT_THROTTLE_NONE;
    }

    if (s->published) {
        int64_t dx = (int64_t)target->x_mm - s->x_mm;
        int64_t dy = (int64_t)target->y_mm - s->y_mm;
        int64_t thr = (int64_t)t->threshold_mm * t->threshold_mm;
        if (dx * dx + dy * dy < thr) {
            return MQTT_THROTTLE_NONE;
        }
    }

    s->published = true;
    s->x_mm = target->x_mm;
    s->y_mm = target->y_mm;
    return MQTT_THROTTLE_MOVED;
}
```

- [x] **Step 5: Run the tests to verify they pass**

Same command as Step 3. Expected: `all tests passed`.

- [x] **Step 6: Register in the firmware build and ignore the test binary**

`rd03d_uart/main/CMakeLists.txt` SRCS becomes:

```cmake
idf_component_register(SRCS "main.c" "rd03d.c" "wifi_link.c" "web_server.c" "ota_update.c" "mqtt_throttle.c"
                    INCLUDE_DIRS ""
                    EMBED_FILES "index.html")
```

Append to the repo-root `.gitignore` under the rd03d block:

```
rd03d_uart/tests/test_mqtt_throttle
```

Verify the firmware still builds: `cd rd03d_uart && source ~/esp/esp-idf-v5.5/export.sh && idf.py build` → `Project build complete.`

Also re-run the parser tests (regression): `cd rd03d_uart/tests && cc -Wall -Wextra -o test_rd03d test_rd03d.c ../main/rd03d.c && ./test_rd03d` → `all tests passed`.

- [x] **Step 7: Commit**

```bash
git add rd03d_uart/main/mqtt_throttle.h rd03d_uart/main/mqtt_throttle.c rd03d_uart/tests/test_mqtt_throttle.c rd03d_uart/main/CMakeLists.txt .gitignore
git commit -m "feat(rd03d_uart): movement-threshold throttle core with host tests"
```

End every commit message in this plan with:
`Co-Authored-By: Claude Fable 5 <noreply@anthropic.com>`

---

### Task 2: MQTT client module + wiring — delivered via OTA

**Files:**
- Modify: `rd03d_uart/main/Kconfig.projbuild`
- Create: `rd03d_uart/main/mqtt_pub.h`
- Create: `rd03d_uart/main/mqtt_pub.c`
- Modify: `rd03d_uart/main/main.c`
- Modify: `rd03d_uart/main/CMakeLists.txt`

- [x] **Step 1: Add Kconfig options**

In `rd03d_uart/main/Kconfig.projbuild`, inside the existing `menu "RD03D Configuration"` (before `endmenu`), add:

```
config RD03D_MQTT_HOST
    string "MQTT broker host"
    default "iotstack.local"
    help
        Broker hostname. A .local name is resolved via mDNS by the firmware.

config RD03D_MQTT_PORT
    int "MQTT broker port"
    default 1883

config RD03D_MQTT_MOVE_MM
    int "Minimum movement (mm) between MQTT publishes per target"
    default 200
```

- [x] **Step 2: Create mqtt_pub.h**

`rd03d_uart/main/mqtt_pub.h`:

```c
#pragma once

#include "rd03d.h"

/* Starts the MQTT client: waits for WiFi, resolves the configured broker
 * (mDNS for .local names), connects with a Last-Will on rd03d/status, and
 * auto-reconnects. Safe to call once at boot. */
void mqtt_pub_start(void);

/* Publish per-target movement/gone events for a parsed frame, throttled by
 * the configured minimum movement. No-op while disconnected; never blocks
 * meaningfully (QoS 0, esp-mqtt handles the socket). */
void mqtt_pub_frame(const rd03d_frame_t *f);
```

- [x] **Step 3: Create mqtt_pub.c**

`rd03d_uart/main/mqtt_pub.c`:

```c
#include "mqtt_pub.h"

#include <stdio.h>
#include <string.h>

#include "freertos/FreeRTOS.h"
#include "freertos/task.h"
#include "esp_log.h"
#include "mdns.h"
#include "mqtt_client.h"
#include "sdkconfig.h"

#include "mqtt_throttle.h"
#include "wifi_link.h"

static const char *TAG = "mqtt_pub";

#define STATUS_TOPIC        "rd03d/status"
#define RESOLVE_RETRY_MS    30000
#define MQTT_KEEPALIVE_S    15  /* short keepalive so the LWT fires quickly */

static esp_mqtt_client_handle_t s_client;
static volatile bool s_connected;
static mqtt_throttle_t s_throttle;

static void on_mqtt_event(void *arg, esp_event_base_t base, int32_t id,
                          void *data)
{
    (void)arg;
    (void)base;
    (void)data;
    if (id == MQTT_EVENT_CONNECTED) {
        mqtt_throttle_reset(&s_throttle); /* republish current targets */
        s_connected = true;
        esp_mqtt_client_publish(s_client, STATUS_TOPIC, "online", 0, 0, 1);
        ESP_LOGI(TAG, "connected to broker");
    } else if (id == MQTT_EVENT_DISCONNECTED) {
        s_connected = false;
        ESP_LOGW(TAG, "disconnected from broker");
    }
}

/* esp-mqtt resolves via plain DNS, which cannot see mDNS names — resolve
 * .local hosts ourselves through the already-running mDNS stack. */
static bool resolve_broker_uri(char *uri, size_t uri_len)
{
    const char *host = CONFIG_RD03D_MQTT_HOST;
    const char *suffix = ".local";
    size_t hlen = strlen(host);
    size_t slen = strlen(suffix);

    if (hlen > slen && strcmp(host + hlen - slen, suffix) == 0) {
        char name[64];
        if (hlen - slen >= sizeof(name)) {
            ESP_LOGE(TAG, "broker hostname too long");
            return false;
        }
        memcpy(name, host, hlen - slen);
        name[hlen - slen] = '\0';

        esp_ip4_addr_t addr = { 0 };
        esp_err_t err = mdns_query_a(name, 3000, &addr);
        if (err != ESP_OK) {
            ESP_LOGW(TAG, "mdns query for %s failed: %s", host,
                     esp_err_to_name(err));
            return false;
        }
        snprintf(uri, uri_len, "mqtt://" IPSTR ":%d", IP2STR(&addr),
                 CONFIG_RD03D_MQTT_PORT);
    } else {
        snprintf(uri, uri_len, "mqtt://%s:%d", host, CONFIG_RD03D_MQTT_PORT);
    }
    return true;
}

static void mqtt_connect_task(void *arg)
{
    (void)arg;
    while (!wifi_link_has_ip()) {
        vTaskDelay(pdMS_TO_TICKS(1000));
    }

    char uri[96];
    while (!resolve_broker_uri(uri, sizeof(uri))) {
        vTaskDelay(pdMS_TO_TICKS(RESOLVE_RETRY_MS));
    }
    ESP_LOGI(TAG, "broker: %s", uri);

    const esp_mqtt_client_config_t cfg = {
        .broker.address.uri = uri,
        .session = {
            .keepalive = MQTT_KEEPALIVE_S,
            .last_will = {
                .topic = STATUS_TOPIC,
                .msg = "offline",
                .qos = 0,
                .retain = 1,
            },
        },
    };
    s_client = esp_mqtt_client_init(&cfg); /* config strings are copied */
    if (s_client == NULL) {
        ESP_LOGE(TAG, "mqtt client init failed; MQTT unavailable");
        vTaskDelete(NULL);
        return;
    }
    ESP_ERROR_CHECK(esp_mqtt_client_register_event(s_client, ESP_EVENT_ANY_ID,
                                                   on_mqtt_event, NULL));
    ESP_ERROR_CHECK(esp_mqtt_client_start(s_client));
    vTaskDelete(NULL);
}

void mqtt_pub_start(void)
{
    mqtt_throttle_init(&s_throttle, CONFIG_RD03D_MQTT_MOVE_MM);
    xTaskCreate(mqtt_connect_task, "mqtt_connect", 4096, NULL, 5, NULL);
}

void mqtt_pub_frame(const rd03d_frame_t *f)
{
    if (!s_connected) {
        return;
    }
    for (int i = 0; i < RD03D_NUM_TARGETS; i++) {
        mqtt_throttle_action_t act =
            mqtt_throttle_eval(&s_throttle, i, &f->targets[i]);
        if (act == MQTT_THROTTLE_NONE) {
            continue;
        }
        char topic[24];
        snprintf(topic, sizeof(topic), "rd03d/target/%d", i + 1);
        if (act == MQTT_THROTTLE_MOVED) {
            char payload[64];
            int n = snprintf(payload, sizeof(payload),
                             "{\"x\":%d,\"y\":%d,\"v\":%d}",
                             f->targets[i].x_mm, f->targets[i].y_mm,
                             f->targets[i].speed_cms);
            if (n > 0 && n < (int)sizeof(payload)) {
                esp_mqtt_client_publish(s_client, topic, payload, n, 0, 0);
            }
        } else { /* MQTT_THROTTLE_GONE */
            esp_mqtt_client_publish(s_client, topic, "{\"gone\":true}", 0, 0,
                                    0);
        }
    }
}
```

- [x] **Step 4: Wire into main.c**

In `rd03d_uart/main/main.c`:

(a) add with the other includes:

```c
#include "mqtt_pub.h"
```

(b) in `app_main`, directly after the `xTaskCreate(ota_validation_task, ...)` line, add:

```c
    mqtt_pub_start();
```

(c) in the parse branch, directly after the `web_server_send_frame(...)` call, add:

```c
                mqtt_pub_frame(&frame);
```

- [x] **Step 5: Register the source file**

`rd03d_uart/main/CMakeLists.txt` SRCS becomes:

```cmake
idf_component_register(SRCS "main.c" "rd03d.c" "wifi_link.c" "web_server.c" "ota_update.c" "mqtt_throttle.c" "mqtt_pub.c"
                    INCLUDE_DIRS ""
                    EMBED_FILES "index.html")
```

- [x] **Step 6: Commit BEFORE building (clean version stamp)**

```bash
git add rd03d_uart/main/Kconfig.projbuild rd03d_uart/main/mqtt_pub.h rd03d_uart/main/mqtt_pub.c rd03d_uart/main/main.c rd03d_uart/main/CMakeLists.txt
git commit -m "feat(rd03d_uart): publish throttled target events to MQTT"
```

(If `git status --porcelain -uno` shows other dirty files — e.g. this plan — stash them around the build in the next step.)

- [x] **Step 7: Build and deliver via OTA**

```bash
cd rd03d_uart && source ~/esp/esp-idf-v5.5/export.sh && idf.py build && curl -X POST --max-time 120 --data-binary @build/rd03d_uart.bin http://192.168.1.186/update
```

Expected: build clean (the new Kconfig symbols pick up their defaults automatically; no warnings in the new files), then `update ok, rebooting`.

- [x] **Step 8: Verify connection**

Wait ~25 s, then `curl -s --max-time 10 http://192.168.1.186/version` → the new commit's short hash. Console capture (~15 s, pyserial /dev/cu.usbmodem11101 @115200, DTR/RTS low — resets the board, which is fine and lets you see the whole boot):

Expected lines, in order: boot → wifi `got ip` → `mqtt_pub: broker: mqtt://<some-ip>:1883` → `mqtt_pub: connected to broker` → radar frames continuing, `dropped=0`.

If instead `mdns query for iotstack.local failed` repeats every 30 s: the broker box may be down — report BLOCKED with the log (the rest of the firmware must still be running normally).

---

### Task 3: Behavior verification against the live broker

No code changes; no commits except plan checkboxes.

- [x] **Step 1: Set up a subscriber on the Mac**

```bash
SP=/private/tmp/claude-501/-path-to-rd03d/1a58ef3a-b659-4aae-a07a-3f6d1a6f573b/scratchpad
$SP/venv/bin/pip install -q paho-mqtt && $SP/venv/bin/python - <<'EOF'
import time
import paho.mqtt.client as mqtt

msgs = []
def on_message(c, u, m):
    line = f"{time.strftime('%H:%M:%S')} {m.topic} {m.payload.decode()} retain={m.retain}"
    msgs.append(line)
    print(line, flush=True)

c = mqtt.Client(mqtt.CallbackAPIVersion.VERSION2)
c.on_message = on_message
c.connect("iotstack.local", 1883, 30)
c.subscribe("rd03d/#")
c.loop_start()
time.sleep(45)
c.loop_stop()
print(f"total: {len(msgs)} messages")
EOF
```

(If `iotstack.local` fails to resolve from Python, substitute the broker's IP.)

- [x] **Step 2: Interpret the capture**

Expected during the 45 s window (someone/something moving in front of the radar helps — the user at their desk usually suffices):
- Immediately: `rd03d/status online retain=1` (retained → arrives on subscribe).
- `rd03d/target/N {"x":...,"y":...,"v":...}` messages whose cadence tracks motion: bursts while moving, **silence while still** (this is the throttle working — compare against the ~11 Hz WebSocket rate).
- If a target left during the window: `rd03d/target/N {"gone":true}`.
- Sanity: coordinates within the radar's range (|x| ≤ 8000, 0 ≤ y ≤ 8000).

- [x] **Step 3: LWT drill (no hands needed)**

Re-upload the SAME already-built firmware to force an abrupt reboot (esp_restart does not close the TCP connection gracefully, so the broker must fire the Last-Will within ~1.5 × the 15 s keepalive):

Start the subscriber again (60 s window this time) in the background or a second step, then:

```bash
curl -X POST --max-time 120 --data-binary @rd03d_uart/build/rd03d_uart.bin http://192.168.1.186/update
```

Expected in the subscriber output: `rd03d/status offline retain=1` within ~25 s of the reboot, followed by `rd03d/status online retain=1` when the device reconnects, followed by fresh `rd03d/target/N` messages for currently-present targets (the reconnect republish). Note: the device reboots into the OTHER slot running identical firmware — harmless.

- [x] **Step 4: Stand-still silence check**

One more 30 s subscriber run while nothing moves in front of the radar (or the user sits still): expect ZERO `rd03d/target` messages (status may replay as retained). If messages trickle in while genuinely still, note the observed coordinate jitter amplitude in the report — the 200 mm threshold should swallow radar noise by a wide margin.

---

### Task 4: Documentation

**Files:**
- Modify: `rd03d_uart/README.md`

- [x] **Step 1: Add the MQTT section**

In `rd03d_uart/README.md`, after the "## OTA firmware updates" section, add:

```markdown
## MQTT events

The firmware publishes to the broker configured in `idf.py menuconfig`
(*RD03D Configuration*, default `iotstack.local:1883`, anonymous):

- `rd03d/target/1..3` — `{"x":-551,"y":550,"v":0}` when that target first
  appears or has moved ≥ the configured distance (default 200 mm) since the
  last published position; `{"gone":true}` once when it disappears.
  QoS 0, not retained.
- `rd03d/status` — retained `online`/`offline` (Last-Will), so consumers
  (e.g. Node-RED) always know whether the sensor is alive.

While the broker is unreachable nothing is queued; on (re)connect the device
republishes `online` and the current position of every present target.
```

- [x] **Step 2: Commit**

```bash
git add rd03d_uart/README.md
git commit -m "docs(rd03d_uart): document MQTT topics and throttle semantics"
```
