nThanksForAllTheFish/rd03d/docs/superpowers/plans/2026-09-06-rd03d-ota.md

# RD-03D OTA Updates Implementation Plan

> **For agentic workers:** REQUIRED SUB-SKILL: Use superpowers:subagent-driven-development (recommended) or superpowers:executing-plans to implement this plan task-by-task. Steps use checkbox (`- [ ]`) syntax for tracking.

**Goal:** Push firmware updates to the wall-mounted XIAO over WiFi (browser page or one curl), with two OTA slots and automatic bootloader rollback so a bad update always falls back to the previous working firmware.

**Architecture:** One-time USB migration to a 4 MB / two-slot partition table with `CONFIG_BOOTLOADER_APP_ROLLBACK_ENABLE`. New `ota_update` module registers `GET/POST /update` on the existing esp_http_server (streams the body into the passive slot via `esp_ota_begin/write/end`). A validation task in `main.c` marks a pending image valid only once WiFi has an IP and the web server is up; otherwise it restarts at 90 s and the bootloader reverts. `GET /version` + a HUD line surface the running build (ESP-IDF already stamps `esp_app_desc` from `git describe`).

**Tech Stack:** ESP-IDF v5.5 (`~/esp/esp-idf-v5.5`): app_update (`esp_ota_ops`), esp_app_desc, esp_http_server, custom `partitions.csv`.

**Spec:** `docs/superpowers/specs/2026-09-06-rd03d-ota-design.md`

**Environment (every build shell):** `source ~/esp/esp-idf-v5.5/export.sh`, combined with idf.py commands on one line (fresh shell per Bash call). Serial port `/dev/cu.usbmodem11101` (`ls /dev/cu.usbmodem*` if missing). Device: `rd03d.local` / 192.168.1.186. `main/rd03d.c/.h` must not change. WiFi credentials live only in the untracked `rd03d_uart/sdkconfig`; the controller supplies them when a task must regenerate that file — they never appear in committed files, this plan, or reports.

**Task ordering note:** Task 2's flash is the LAST required USB flash. Task 3 is deliberately delivered *via OTA* — it is the happy-path test.

---

### Task 1: Partition migration to two OTA slots (USB, one-time)

**Files:**
- Create: `rd03d_uart/partitions.csv`
- Modify: `rd03d_uart/sdkconfig.defaults`
- Regenerate (untracked): `rd03d_uart/sdkconfig`

- [x] **Step 1: Create the partition table**

`rd03d_uart/partitions.csv`:

```
# Name,   Type, SubType,  Offset,   Size
nvs,      data, nvs,      0x9000,   0x6000
otadata,  data, ota,      0xf000,   0x2000
phy_init, data, phy,      0x11000,  0x1000
ota_0,    app,  ota_0,    0x20000,  0x180000
ota_1,    app,  ota_1,    0x1A0000, 0x180000
```

(Two 1.5 MB slots; app is ~0.96 MB. Ends at 0x320000, leaving 896 KB of the
4 MB chip spare for a future data partition.)

- [x] **Step 2: Update sdkconfig.defaults**

Replace the whole `rd03d_uart/sdkconfig.defaults` with:

```
CONFIG_IDF_TARGET="esp32c6"
CONFIG_ESP_CONSOLE_USB_SERIAL_JTAG=y
CONFIG_HTTPD_WS_SUPPORT=y
CONFIG_ESPTOOLPY_FLASHSIZE_4MB=y
CONFIG_PARTITION_TABLE_CUSTOM=y
CONFIG_PARTITION_TABLE_CUSTOM_FILENAME="partitions.csv"
CONFIG_BOOTLOADER_APP_ROLLBACK_ENABLE=y
```

- [x] **Step 3: Regenerate sdkconfig and restore credentials**

Defaults don't retro-apply, so regenerate (the WiFi credentials are supplied by
the controller — NEVER commit them or echo the password):

```bash
cd rd03d_uart && rm sdkconfig && source ~/esp/esp-idf-v5.5/export.sh && idf.py reconfigure >/dev/null && sed -i '' 's/^CONFIG_RD03D_WIFI_SSID=.*/CONFIG_RD03D_WIFI_SSID="<SSID-FROM-CONTROLLER>"/' sdkconfig && sed -i '' 's/^CONFIG_RD03D_WIFI_PASSWORD=.*/CONFIG_RD03D_WIFI_PASSWORD="<PASSWORD-FROM-CONTROLLER>"/' sdkconfig && grep -E "FLASHSIZE_4MB|PARTITION_TABLE_CUSTOM=|APP_ROLLBACK" sdkconfig
```

Expected grep: `CONFIG_ESPTOOLPY_FLASHSIZE_4MB=y`, `CONFIG_PARTITION_TABLE_CUSTOM=y`, `CONFIG_BOOTLOADER_APP_ROLLBACK_ENABLE=y`.

- [x] **Step 4: Build, erase, flash (the migration)**

```bash
cd rd03d_uart && source ~/esp/esp-idf-v5.5/export.sh && idf.py build && idf.py -p /dev/cu.usbmodem11101 erase-flash flash
```

Expected: build lists the new partition table (ota_0/ota_1); erase + flash complete with hash verification.

- [x] **Step 5: Verify on hardware**

Capture ~12 s of console (pyserial: open /dev/cu.usbmodem11101 @115200, DTR/RTS low, read, print). Expected:
- Boot log partition table shows `ota_0` and `ota_1`; a line like `boot: Loaded app from partition at offset 0x20000` (= ota_0).
- WiFi joins, `got ip`, mdns line, radar `T1:` frames, `dropped=0`.

Then from the Mac: `curl -s --max-time 10 http://192.168.1.186/ | head -3` returns the chart page, and the WebSocket check (scratchpad venv `websockets`, 5 messages from `ws://192.168.1.186/ws`) still streams JSON.

- [x] **Step 6: Commit**

```bash
git add rd03d_uart/partitions.csv rd03d_uart/sdkconfig.defaults
git commit -m "feat(rd03d_uart): two-slot OTA partition table on 4MB flash"
```

End every commit message in this plan with:
`Co-Authored-By: Claude Fable 5 <noreply@anthropic.com>`

---

### Task 2: OTA endpoint + rollback validation (last USB flash)

**Files:**
- Create: `rd03d_uart/main/ota_update.h`
- Create: `rd03d_uart/main/ota_update.c`
- Modify: `rd03d_uart/main/web_server.h` (+ handle getter)
- Modify: `rd03d_uart/main/web_server.c` (+ handle getter)
- Modify: `rd03d_uart/main/wifi_link.h` (+ has-ip getter)
- Modify: `rd03d_uart/main/wifi_link.c` (+ has-ip state)
- Modify: `rd03d_uart/main/main.c` (register OTA + validation task)
- Modify: `rd03d_uart/main/CMakeLists.txt`

- [x] **Step 1: Expose the server handle**

In `rd03d_uart/main/web_server.h`, add after the existing includes:

```c
#include "esp_http_server.h"
```

and add before `web_server_send_frame`:

```c
/* The running HTTP server handle, or NULL if the server failed to start. */
httpd_handle_t web_server_handle(void);
```

In `rd03d_uart/main/web_server.c`, add after `web_server_start` (before `web_server_send_frame`):

```c
httpd_handle_t web_server_handle(void)
{
    return s_server;
}
```

- [x] **Step 2: Expose WiFi connection state**

In `rd03d_uart/main/wifi_link.h`, add `#include <stdbool.h>` at the top (after `#pragma once`) and, after `wifi_link_start`:

```c
/* True while the station holds an IP address. */
bool wifi_link_has_ip(void);
```

In `rd03d_uart/main/wifi_link.c`:

(a) after `static const char *TAG = "wifi_link";` add:

```c
static volatile bool s_has_ip;
```

(b) in `on_wifi_event`, set the flag: in the `WIFI_EVENT_STA_DISCONNECTED` branch, add `s_has_ip = false;` as the first line; in the `IP_EVENT_STA_GOT_IP` branch, add `s_has_ip = true;` before the log line.

(c) at the end of the file add:

```c
bool wifi_link_has_ip(void)
{
    return s_has_ip;
}
```

- [x] **Step 3: Create ota_update.h**

`rd03d_uart/main/ota_update.h`:

```c
#pragma once

#include "esp_http_server.h"

/* Registers GET /update (upload page) and POST /update (firmware upload)
 * on an already-started HTTP server. NULL server -> logs and does nothing. */
void ota_update_register(httpd_handle_t server);
```

- [x] **Step 4: Create ota_update.c**

`rd03d_uart/main/ota_update.c`:

```c
#include "ota_update.h"

#include <stdio.h>
#include <string.h>

#include "freertos/FreeRTOS.h"
#include "freertos/task.h"
#include "esp_app_desc.h"
#include "esp_log.h"
#include "esp_ota_ops.h"
#include "esp_system.h"

static const char *TAG = "ota_update";

static bool s_upload_in_progress;

static const char UPDATE_PAGE_FMT[] =
"<!DOCTYPE html><html><head><meta charset=\"utf-8\">"
"<meta name=\"viewport\" content=\"width=device-width, initial-scale=1\">"
"<title>rd03d update</title></head>"
"<body style=\"font-family:system-ui;background:#121212;color:#ddd;padding:24px\">"
"<h2>rd03d firmware update</h2>"
"<p>Running: %s (slot %s)</p>"
"<input type=\"file\" id=\"f\" accept=\".bin\"> "
"<button onclick=\"up()\">Upload</button>"
"<a href=\"/\" style=\"color:#00b4ff\">back to chart</a>"
"<script>async function up(){const f=document.getElementById('f').files[0];"
"const s=document.getElementById('s');if(!f){s.textContent='pick a .bin first';return;}"
"s.textContent='uploading '+f.name+' ('+f.size+' bytes)...';"
"try{const r=await fetch('/update',{method:'POST',body:f});"
"s.textContent=await r.text();}catch(e){s.textContent='upload failed: '+e;}}"
"</script></body></html>";

static esp_err_t update_get(httpd_req_t *req)
{
    const esp_app_desc_t *app = esp_app_get_description();
    const esp_partition_t *running = esp_ota_get_running_partition();
    char page[sizeof(UPDATE_PAGE_FMT) + 96];
    int n = snprintf(page, sizeof(page), UPDATE_PAGE_FMT,
                     app->version, running ? running->label : "?");
    if (n < 0 || n >= (int)sizeof(page)) {
        return httpd_resp_send_500(req);
    }
    httpd_resp_set_type(req, "text/html");
    return httpd_resp_send(req, page, n);
}

static void restart_task(void *arg)
{
    (void)arg;
    vTaskDelay(pdMS_TO_TICKS(1000)); /* let the HTTP response flush */
    esp_restart();
}

static esp_err_t update_post(httpd_req_t *req)
{
    if (s_upload_in_progress) {
        httpd_resp_set_status(req, "409 Conflict");
        httpd_resp_sendstr(req, "another upload is in progress\n");
        return ESP_OK;
    }
    s_upload_in_progress = true;

    const esp_partition_t *target = esp_ota_get_next_update_partition(NULL);
    esp_ota_handle_t ota = 0;
    esp_err_t err = (target == NULL) ? ESP_ERR_NOT_FOUND : ESP_OK;

    if (err == ESP_OK &&
        (req->content_len == 0 || req->content_len > target->size)) {
        err = ESP_ERR_INVALID_SIZE;
    }
    if (err == ESP_OK) {
        ESP_LOGI(TAG, "OTA start: %u bytes -> %s",
                 (unsigned)req->content_len, target->label);
        err = esp_ota_begin(target, req->content_len, &ota);
    }

    /* Single-flight upload (guarded above), so a static buffer is safe and
     * keeps the httpd task's small stack out of trouble. */
    static char buf[4096];
    size_t remaining = (err == ESP_OK) ? req->content_len : 0;
    while (err == ESP_OK && remaining > 0) {
        int n = httpd_req_recv(req, buf,
                               remaining < sizeof(buf) ? remaining
                                                       : sizeof(buf));
        if (n <= 0) {
            err = ESP_FAIL; /* client gone or receive timeout */
            break;
        }
        err = esp_ota_write(ota, buf, (size_t)n);
        remaining -= (size_t)n;
    }

    if (err == ESP_OK) {
        err = esp_ota_end(ota); /* verifies image magic + hash */
        ota = 0;
    } else if (ota != 0) {
        esp_ota_abort(ota);
        ota = 0;
    }
    if (err == ESP_OK) {
        err = esp_ota_set_boot_partition(target);
    }

    s_upload_in_progress = false;

    if (err != ESP_OK) {
        ESP_LOGW(TAG, "OTA failed: %s", esp_err_to_name(err));
        char msg[96];
        snprintf(msg, sizeof(msg), "update failed: %s\n",
                 esp_err_to_name(err));
        httpd_resp_set_status(req, "400 Bad Request");
        httpd_resp_sendstr(req, msg);
        return ESP_OK;
    }

    ESP_LOGI(TAG, "OTA ok, rebooting into %s", target->label);
    httpd_resp_sendstr(req, "update ok, rebooting\n");
    xTaskCreate(restart_task, "ota_restart", 2048, NULL, 5, NULL);
    return ESP_OK;
}

void ota_update_register(httpd_handle_t server)
{
    if (server == NULL) {
        ESP_LOGE(TAG, "no http server; OTA unavailable");
        return;
    }
    static const httpd_uri_t get_uri = {
        .uri = "/update",
        .method = HTTP_GET,
        .handler = update_get,
    };
    static const httpd_uri_t post_uri = {
        .uri = "/update",
        .method = HTTP_POST,
        .handler = update_post,
    };
    ESP_ERROR_CHECK(httpd_register_uri_handler(server, &get_uri));
    ESP_ERROR_CHECK(httpd_register_uri_handler(server, &post_uri));
    ESP_LOGI(TAG, "OTA endpoint ready at /update");
}
```

- [x] **Step 5: Validation task + wiring in main.c**

In `rd03d_uart/main/main.c`:

(a) add includes with the others:

```c
#include "esp_ota_ops.h"
#include "ota_update.h"
```

(b) add with the other #defines:

```c
#define OTA_VALID_DEADLINE_MS 90000
```

(c) add after `print_frame` (before `app_main`):

```c
/* A freshly-OTA'd image boots pending-verify. Mark it valid only once the
 * device is provably updatable again (WiFi up + web server running); if that
 * never happens, restart while still pending so the bootloader rolls back
 * to the previous firmware. USB-flashed images are never pending: no-op. */
static void ota_validation_task(void *arg)
{
    (void)arg;
    const esp_partition_t *running = esp_ota_get_running_partition();
    esp_ota_img_states_t state;
    if (esp_ota_get_state_partition(running, &state) != ESP_OK ||
        state != ESP_OTA_IMG_PENDING_VERIFY) {
        vTaskDelete(NULL);
        return;
    }
    TickType_t deadline =
        xTaskGetTickCount() + pdMS_TO_TICKS(OTA_VALID_DEADLINE_MS);
    while ((int32_t)(deadline - xTaskGetTickCount()) > 0) {
        if (wifi_link_has_ip() && web_server_handle() != NULL) {
            ESP_ERROR_CHECK(esp_ota_mark_app_valid_cancel_rollback());
            ESP_LOGI(TAG, "firmware validated (WiFi + web server up)");
            vTaskDelete(NULL);
            return;
        }
        vTaskDelay(pdMS_TO_TICKS(1000));
    }
    ESP_LOGE(TAG, "validation deadline missed - restarting to roll back");
    esp_restart();
}
```

(d) in `app_main`, directly after the `web_server_start();` line, add:

```c
    ota_update_register(web_server_handle());
    xTaskCreate(ota_validation_task, "ota_valid", 3072, NULL, 5, NULL);
```

- [x] **Step 6: Register the source file**

`rd03d_uart/main/CMakeLists.txt` becomes:

```cmake
idf_component_register(SRCS "main.c" "rd03d.c" "wifi_link.c" "web_server.c" "ota_update.c"
                    INCLUDE_DIRS ""
                    EMBED_FILES "index.html")
```

- [x] **Step 7: Build and flash (LAST USB flash)**

```bash
cd rd03d_uart && source ~/esp/esp-idf-v5.5/export.sh && idf.py build && idf.py -p /dev/cu.usbmodem11101 flash
```

Expected: clean build (no warnings in new/modified files), flash OK.

- [x] **Step 8: Verify**

- `curl -s --max-time 10 http://192.168.1.186/update` → the upload page HTML, showing the running version and slot `ota_0`.
- Console capture ~12 s: boot log shows `OTA endpoint ready at /update`; no validation log (USB image is not pending-verify — the task exits silently); radar frames + WiFi as before.
- Host parser regression: `cd rd03d_uart/tests && cc -Wall -Wextra -o test_rd03d test_rd03d.c ../main/rd03d.c && ./test_rd03d` → `all tests passed`.

- [x] **Step 9: Commit**

```bash
git add rd03d_uart/main/ota_update.h rd03d_uart/main/ota_update.c rd03d_uart/main/web_server.h rd03d_uart/main/web_server.c rd03d_uart/main/wifi_link.h rd03d_uart/main/wifi_link.c rd03d_uart/main/main.c rd03d_uart/main/CMakeLists.txt
git commit -m "feat(rd03d_uart): OTA upload endpoint with bootloader rollback"
```

---

### Task 3: Version visibility — delivered via OTA (the happy-path test)

**Files:**
- Modify: `rd03d_uart/main/web_server.c` (+ /version)
- Modify: `rd03d_uart/main/index.html` (+ HUD version)

- [x] **Step 1: Add the /version endpoint**

In `rd03d_uart/main/web_server.c`:

(a) add `#include "esp_app_desc.h"` with the other includes.

(b) add after `ws_get` (before `ws_send_work`):

```c
static esp_err_t version_get(httpd_req_t *req)
{
    httpd_resp_set_type(req, "text/plain");
    return httpd_resp_sendstr(req, esp_app_get_description()->version);
}
```

(c) in `web_server_start`, after the two existing registrations, add:

```c
    static const httpd_uri_t version_uri = {
        .uri = "/version",
        .method = HTTP_GET,
        .handler = version_get,
    };
    ESP_ERROR_CHECK(httpd_register_uri_handler(s_server, &version_uri));
```

- [x] **Step 2: Show it in the chart HUD**

In `rd03d_uart/main/index.html`:

(a) in the `#hud` div, after `<span id="stats"></span>`, add:

```html
  <span id="ver" style="color:#777"></span>
```

(b) at the end of the script, just before `resize();`, add:

```js
fetch("/version")
  .then(function (r) { return r.text(); })
  .then(function (v) { document.getElementById("ver").textContent = "fw " + v; })
  .catch(function () {});
```

- [x] **Step 3: Commit FIRST (so the version stamp is clean, not -dirty)**

```bash
git add rd03d_uart/main/web_server.c rd03d_uart/main/index.html
git commit -m "feat(rd03d_uart): show firmware version via /version and chart HUD"
```

- [x] **Step 4: Build and deliver via OTA**

```bash
cd rd03d_uart && source ~/esp/esp-idf-v5.5/export.sh && idf.py build && curl -X POST --max-time 120 --data-binary @build/rd03d_uart.bin http://192.168.1.186/update
```

Expected curl response: `update ok, rebooting`.

- [x] **Step 5: Verify the OTA took**

Wait ~20 s for reboot + WiFi join, then:

```bash
curl -s --max-time 10 http://192.168.1.186/version && echo && curl -s --max-time 10 http://192.168.1.186/update | grep -o "slot ota_[01]"
```

Expected: the version equals the new commit's short hash (compare `git rev-parse --short HEAD`; suffix formatting may differ slightly — it must differ from the previous version and not say `-dirty`), and the slot is now `ota_1`. Console capture (if USB still attached) additionally shows `firmware validated (WiFi + web server up)`. The chart page HUD shows `fw <version>`.

- [x] **Step 6: Browser-path check (user or controller)**

Open `http://rd03d.local/update` in a browser: the page shows the new version and slot. (An actual browser-upload round-trip is exercised implicitly by the same handler curl used; a full browser upload can be done at the user's leisure on any future update.)

---

### Task 4: Rollback drill + bad-file drill (no code changes)

Nothing is committed in this task except plan checkboxes. The credentials
placeholder values come from the controller.

- [x] **Step 1: Bad-file drill**

```bash
echo "this is not firmware" > /tmp/notfw.txt && curl -s -X POST --data-binary @/tmp/notfw.txt http://192.168.1.186/update
```

Expected: `update failed: ...` (an esp_err name; image header validation fails on first write). Then confirm the device is untouched: `curl -s http://192.168.1.186/version` returns the same version, chart still streams.

- [x] **Step 2: Build a deliberately-bad image (wrong SSID)**

```bash
cd rd03d_uart && sed -i '' 's/^CONFIG_RD03D_WIFI_SSID=.*/CONFIG_RD03D_WIFI_SSID="no-such-network"/' sdkconfig && source ~/esp/esp-idf-v5.5/export.sh && idf.py build
```

- [x] **Step 3: Upload it and watch the rollback**

Record the current version first (`curl -s http://192.168.1.186/version`), then:

```bash
curl -X POST --max-time 120 --data-binary @rd03d_uart/build/rd03d_uart.bin http://192.168.1.186/update
```

The device reboots into the bad image, cannot join WiFi, hits the 90 s validation deadline, restarts, and the bootloader reverts. After ~3 minutes total:

```bash
sleep 180 && curl -s --max-time 15 http://192.168.1.186/version
```

Expected: the OLD version string — the device recovered by itself. (If USB is attached, the console shows the whole story: `disconnected, retrying` loop → `validation deadline missed - restarting to roll back` → reboot → old version banner.)

- [x] **Step 4: Restore correct credentials and rebuild**

```bash
cd rd03d_uart && sed -i '' 's/^CONFIG_RD03D_WIFI_SSID=.*/CONFIG_RD03D_WIFI_SSID="<SSID-FROM-CONTROLLER>"/' sdkconfig && source ~/esp/esp-idf-v5.5/export.sh && idf.py build
```

(No need to re-upload — the device is already running the good firmware; this
just leaves the working tree's sdkconfig correct for future builds. Verify with
`grep RD03D_WIFI_SSID sdkconfig`.)

---

### Task 5: Documentation

**Files:**
- Modify: `rd03d_uart/README.md`

- [x] **Step 1: Add the OTA section**

In `rd03d_uart/README.md`, after the "## WiFi + web UI" section, add:

```markdown
## OTA firmware updates

The device carries two firmware slots with automatic rollback — a bad update
reverts to the previous firmware by itself (it must join WiFi and start the
web server within 90 s to become permanent).

Update over WiFi (no USB needed):

```bash
idf.py build
curl -X POST --data-binary @build/rd03d_uart.bin http://rd03d.local/update
```

or open **http://rd03d.local/update** in a browser and upload
`build/rd03d_uart.bin`. The running version shows at `/version`, on the
update page, and in the chart HUD.

USB flashing is only needed for first-time setup (partition table changes
require `idf.py erase-flash flash`).
```

- [x] **Step 2: Commit**

```bash
git add rd03d_uart/README.md
git commit -m "docs(rd03d_uart): document OTA updates"
```
