nThanksForAllTheFish/rd03d/docs/superpowers/plans/2026-09-06-rd03d-wifi.md

# RD-03D WiFi Streaming Implementation Plan

> **For agentic workers:** REQUIRED SUB-SKILL: Use superpowers:subagent-driven-development (recommended) or superpowers:executing-plans to implement this plan task-by-task. Steps use checkbox (`- [ ]`) syntax for tracking.

**Goal:** The XIAO ESP32-C6 joins home WiFi, advertises itself as `rd03d.local`, and serves a live radar chart web page (canvas XY plot fed by parsed-JSON WebSocket messages) so any browser — Mac or phone — can view targets with no Processing sketch.

**Architecture:** `wifi_link` (station + reconnect + mDNS) and `web_server` (esp_http_server: `GET /` serves an embedded self-contained HTML page, `GET /ws` pushes one JSON message per parsed radar frame via `httpd_queue_work`, multiple clients, stalled clients dropped). `main.c` sends the radar's multi-target command at boot (done) and calls `web_server_send_frame` after each parsed frame. The Processing sketch is untouched (keeps its USB serial mode).

**Tech Stack:** ESP-IDF v5.5 (`~/esp/esp-idf-v5.5`), esp_wifi/esp_netif/NVS, `espressif/mdns` managed component, esp_http_server with WebSocket support, vanilla HTML/JS canvas.

**Spec:** `docs/superpowers/specs/2026-09-06-rd03d-wifi-design.md` (revised: web UI replaced the raw-TCP + Processing network mode after Task 2 landed)

**Environment (every build shell):** `source ~/esp/esp-idf-v5.5/export.sh` (each Bash call is a fresh shell — combine with idf.py commands on one line). Serial port: `/dev/cu.usbmodem11101` (check `ls /dev/cu.usbmodem*` if missing). `main/rd03d.c/.h` must not change. Device IP on this network: 192.168.1.186 (DHCP; prefer `rd03d.local` once Task 3 lands).

**Credentials note:** WiFi SSID/password live only in the untracked, gitignored `rd03d_uart/sdkconfig` (set in Task 2). They must NEVER appear in committed files, the plan, or commit messages.

---

### Task 1: Send the multi-target command at boot — COMPLETE (commit 5e151dd, amended in e73ad84)

- [x] All steps complete: `RD03D_CMD_MULTI_TARGET` sent after UART init with short-write check and post-delay `uart_flush_input` (ACK discard). Hardware-verified: dropped=0, frames streaming.

---

### Task 2: WiFi station module — COMPLETE (commit e73ad84)

- [x] All steps complete: `Kconfig.projbuild` (RD03D_WIFI_SSID/PASSWORD), `wifi_link.h/.c` (NVS + station + auto-reconnect + got-IP log), registered in build, called from `app_main`. Credentials in untracked sdkconfig only. Hardware-verified: joined network, got ip 192.168.1.186, radar frames uninterrupted, dropped=0.

---

### Task 3: mDNS + wifi_link hardening

**Files:**
- Create: `rd03d_uart/main/idf_component.yml`
- Modify: `rd03d_uart/main/wifi_link.c`
- Modify: `.gitignore` (repo root)

- [x] **Step 1: Harden wifi_link.c (amendments from Task 2 code review)**

In `rd03d_uart/main/wifi_link.c`:

(a) After the `static const char *TAG = "wifi_link";` line, add:

```c
/* strlcpy silently truncates; catch oversize credentials at compile time.
 * (sizeof includes the NUL; the driver fields are 32 and 64 bytes.) */
_Static_assert(sizeof(CONFIG_RD03D_WIFI_SSID) <= 32,
               "WiFi SSID longer than 31 chars would be truncated");
_Static_assert(sizeof(CONFIG_RD03D_WIFI_PASSWORD) <= 64,
               "WiFi password longer than 63 chars would be truncated");
```

(b) At the top of `wifi_link_start`, before the NVS init, add:

```c
    if (CONFIG_RD03D_WIFI_SSID[0] == '\0') {
        ESP_LOGE(TAG, "WiFi credentials not set - run idf.py menuconfig "
                      "(RD03D Configuration)");
        return;
    }
```

(c) In the `wifi_config_t sta_cfg` block, after the two `strlcpy` calls, add:

```c
    /* Refuse to associate with an open AP spoofing our SSID. */
    sta_cfg.sta.threshold.authmode = WIFI_AUTH_WPA2_PSK;
```

- [x] **Step 2: Add the mdns managed component**

`rd03d_uart/main/idf_component.yml`:

```yaml
dependencies:
  espressif/mdns: "^1.2"
  idf: ">=5.0"
```

- [x] **Step 3: Initialize mDNS in wifi_link.c**

Add `#include "mdns.h"` after the other includes, and at the END of `wifi_link_start` (after `esp_wifi_start()` and the "wifi starting" log), add:

```c
    ESP_ERROR_CHECK(mdns_init());
    ESP_ERROR_CHECK(mdns_hostname_set("rd03d"));
    ESP_ERROR_CHECK(mdns_instance_name_set("RD-03D radar stream"));

    ESP_LOGI(TAG, "mdns hostname set: rd03d.local");
```

- [x] **Step 4: Build and flash**

```bash
source ~/esp/esp-idf-v5.5/export.sh && cd rd03d_uart && idf.py build && idf.py -p /dev/cu.usbmodem11101 flash
```

Expected: the component manager downloads `espressif/mdns` into `rd03d_uart/managed_components/` and writes `rd03d_uart/dependencies.lock`; clean build; flash OK.

- [x] **Step 5: Verify resolution from the Mac**

Wait ~10 s after flashing (WiFi join), then:

```bash
ping -c 2 rd03d.local
```

Expected: replies from 192.168.1.186. If resolution fails, try `dns-sd -q rd03d.local` for diagnosis; report BLOCKED with output if it never resolves. Also capture ~10 s of console (pyserial snippet from Task 1) to confirm `got ip` still appears and radar frames still stream after the hardening changes.

- [x] **Step 6: Ignore managed-component artifacts and commit**

Append to the repo-root `.gitignore` under the existing rd03d block:

```
rd03d_uart/managed_components/
```

Then:

```bash
git add .gitignore rd03d_uart/main/idf_component.yml rd03d_uart/main/wifi_link.c rd03d_uart/dependencies.lock
git commit -m "feat(rd03d_uart): advertise rd03d.local via mDNS; harden WiFi config"
```

(`dependencies.lock` IS committed — it pins the mdns version, like a package lockfile.)

End every commit message in this plan with:
`Co-Authored-By: Claude Fable 5 <noreply@anthropic.com>`

---

### Task 4: HTTP + WebSocket server pushing parsed JSON

> **As-built deviation (recorded during execution):** the prescribed `ws_get`
> handshake registration (`req->method == HTTP_GET` populating `s_ws_fds`) never
> fired on ESP-IDF v5.5 — the server completes the WS handshake without calling
> the URI handler, so no client was ever registered and no frames were pushed.
> The committed `web_server.c` instead enumerates live sockets on each send via
> `httpd_get_client_list()` + `httpd_ws_get_fd_info()`, pushing to every fd in
> `HTTPD_WS_CLIENT_WEBSOCKET` state and closing any whose send fails. The
> "ws client connected" log line therefore does not exist; WS connectivity is
> verified by receiving frames. Public API and JSON format unchanged.

**Files:**
- Create: `rd03d_uart/main/web_server.h`
- Create: `rd03d_uart/main/web_server.c`
- Create: `rd03d_uart/main/index.html` (placeholder; real page in Task 5)
- Modify: `rd03d_uart/main/CMakeLists.txt`
- Modify: `rd03d_uart/main/main.c`
- Modify: `rd03d_uart/sdkconfig.defaults`
- Modify (untracked, NOT committed): `rd03d_uart/sdkconfig` (enable WS support)

- [x] **Step 1: Enable WebSocket support**

Append to `rd03d_uart/sdkconfig.defaults`:

```
CONFIG_HTTPD_WS_SUPPORT=y
```

And flip it in the already-generated untracked sdkconfig (defaults don't retro-apply):

```bash
cd rd03d_uart && sed -i '' 's/^# CONFIG_HTTPD_WS_SUPPORT is not set/CONFIG_HTTPD_WS_SUPPORT=y/' sdkconfig && grep HTTPD_WS_SUPPORT sdkconfig
```

Expected grep output: `CONFIG_HTTPD_WS_SUPPORT=y`

- [x] **Step 2: Create placeholder index.html**

`rd03d_uart/main/index.html`:

```html
<!DOCTYPE html>
<html><head><meta charset="utf-8"><title>rd03d</title></head>
<body><h1>rd03d web server OK</h1><p>Chart UI arrives in the next task.</p></body></html>
```

- [x] **Step 3: Create web_server.h**

`rd03d_uart/main/web_server.h`:

```c
#pragma once

#include <stdint.h>

#include "rd03d.h"

/* Starts the HTTP server: GET / serves the embedded page, GET /ws is a
 * WebSocket that pushes one JSON message per radar frame. */
void web_server_start(void);

/* Formats {"t":[{x,y,v}|null x3],"dropped":N,"bad":N} and sends it to every
 * connected WebSocket client. Never blocks the caller beyond queueing work;
 * clients whose sends fail are dropped. No server/clients -> no-op. */
void web_server_send_frame(const rd03d_frame_t *f, uint32_t dropped,
                           uint32_t bad);
```

- [x] **Step 4: Create web_server.c**

`rd03d_uart/main/web_server.c`:

```c
#include "web_server.h"

#include <inttypes.h>
#include <stdio.h>
#include <stdlib.h>
#include <string.h>

#include "esp_http_server.h"
#include "esp_log.h"

static const char *TAG = "web_server";

extern const uint8_t index_html_start[] asm("_binary_index_html_start");
extern const uint8_t index_html_end[] asm("_binary_index_html_end");

#define MAX_WS_CLIENTS 4

static httpd_handle_t s_server;
static int s_ws_fds[MAX_WS_CLIENTS]; /* -1 = free; touched only on httpd task */

typedef struct {
    char json[192];
} ws_msg_t;

static esp_err_t root_get(httpd_req_t *req)
{
    httpd_resp_set_type(req, "text/html");
    return httpd_resp_send(req, (const char *)index_html_start,
                           index_html_end - index_html_start);
}

static esp_err_t ws_get(httpd_req_t *req)
{
    if (req->method == HTTP_GET) {
        /* Handshake completed by the server; remember the client. */
        int fd = httpd_req_to_sockfd(req);
        for (int i = 0; i < MAX_WS_CLIENTS; i++) {
            if (s_ws_fds[i] == fd) {
                return ESP_OK;
            }
        }
        for (int i = 0; i < MAX_WS_CLIENTS; i++) {
            if (s_ws_fds[i] < 0) {
                s_ws_fds[i] = fd;
                ESP_LOGI(TAG, "ws client connected (fd %d)", fd);
                return ESP_OK;
            }
        }
        ESP_LOGW(TAG, "ws client limit reached, rejecting fd %d", fd);
        return ESP_FAIL;
    }

    /* We are push-only: drain and ignore anything the client sends. */
    httpd_ws_frame_t frame = { 0 };
    esp_err_t ret = httpd_ws_recv_frame(req, &frame, 0);
    if (ret != ESP_OK) {
        return ret;
    }
    if (frame.len > 0) {
        uint8_t *buf = malloc(frame.len);
        if (buf == NULL) {
            return ESP_ERR_NO_MEM;
        }
        frame.payload = buf;
        ret = httpd_ws_recv_frame(req, &frame, frame.len);
        free(buf);
    }
    return ret;
}

/* Runs on the httpd task via httpd_queue_work. */
static void ws_send_work(void *arg)
{
    ws_msg_t *msg = arg;
    httpd_ws_frame_t frame = {
        .final = true,
        .type = HTTPD_WS_TYPE_TEXT,
        .payload = (uint8_t *)msg->json,
        .len = strlen(msg->json),
    };
    for (int i = 0; i < MAX_WS_CLIENTS; i++) {
        int fd = s_ws_fds[i];
        if (fd < 0) {
            continue;
        }
        if (httpd_ws_get_fd_info(s_server, fd) != HTTPD_WS_CLIENT_WEBSOCKET) {
            s_ws_fds[i] = -1; /* client went away; reap the slot */
            continue;
        }
        if (httpd_ws_send_frame_async(s_server, fd, &frame) != ESP_OK) {
            ESP_LOGW(TAG, "ws send failed, dropping fd %d", fd);
            httpd_sess_trigger_close(s_server, fd);
            s_ws_fds[i] = -1;
        }
    }
    free(msg);
}

void web_server_start(void)
{
    for (int i = 0; i < MAX_WS_CLIENTS; i++) {
        s_ws_fds[i] = -1;
    }

    httpd_config_t cfg = HTTPD_DEFAULT_CONFIG();
    if (httpd_start(&s_server, &cfg) != ESP_OK) {
        ESP_LOGE(TAG, "httpd_start failed, web UI unavailable");
        s_server = NULL;
        return;
    }

    static const httpd_uri_t root_uri = {
        .uri = "/",
        .method = HTTP_GET,
        .handler = root_get,
    };
    static const httpd_uri_t ws_uri = {
        .uri = "/ws",
        .method = HTTP_GET,
        .handler = ws_get,
        .is_websocket = true,
    };
    ESP_ERROR_CHECK(httpd_register_uri_handler(s_server, &root_uri));
    ESP_ERROR_CHECK(httpd_register_uri_handler(s_server, &ws_uri));
    ESP_LOGI(TAG, "http server listening on port %d", cfg.server_port);
}

void web_server_send_frame(const rd03d_frame_t *f, uint32_t dropped,
                           uint32_t bad)
{
    if (s_server == NULL) {
        return;
    }
    ws_msg_t *msg = malloc(sizeof(*msg));
    if (msg == NULL) {
        return;
    }

    int off = snprintf(msg->json, sizeof(msg->json), "{\"t\":[");
    for (int i = 0; i < RD03D_NUM_TARGETS; i++) {
        if (off <= 0 || off >= (int)sizeof(msg->json)) {
            break;
        }
        const rd03d_target_t *t = &f->targets[i];
        const char *sep = (i < RD03D_NUM_TARGETS - 1) ? "," : "";
        if (t->present) {
            off += snprintf(msg->json + off, sizeof(msg->json) - (size_t)off,
                            "{\"x\":%d,\"y\":%d,\"v\":%d}%s",
                            t->x_mm, t->y_mm, t->speed_cms, sep);
        } else {
            off += snprintf(msg->json + off, sizeof(msg->json) - (size_t)off,
                            "null%s", sep);
        }
    }
    if (off > 0 && off < (int)sizeof(msg->json)) {
        off += snprintf(msg->json + off, sizeof(msg->json) - (size_t)off,
                        "],\"dropped\":%" PRIu32 ",\"bad\":%" PRIu32 "}",
                        dropped, bad);
    }
    if (off <= 0 || off >= (int)sizeof(msg->json)) {
        free(msg); /* formatting error or truncation: drop this frame */
        return;
    }

    if (httpd_queue_work(s_server, ws_send_work, msg) != ESP_OK) {
        free(msg);
    }
}
```

- [x] **Step 5: Register sources and the embedded page**

`rd03d_uart/main/CMakeLists.txt` becomes:

```cmake
idf_component_register(SRCS "main.c" "rd03d.c" "wifi_link.c" "web_server.c"
                    INCLUDE_DIRS ""
                    EMBED_FILES "index.html")
```

- [x] **Step 6: Wire into main.c**

Add near the other includes:

```c
#include "web_server.h"
```

In `app_main`, directly after the `wifi_link_start();` line, add:

```c
    web_server_start();
```

In the read loop, change the parse branch to also push to the web clients:

```c
        for (int i = 0; i < n; i++) {
            if (rd03d_parser_feed(&parser, buf[i], &frame)) {
                print_frame(&frame);
                web_server_send_frame(&frame, parser.dropped_bytes,
                                      parser.bad_frames);
            }
        }
```

- [x] **Step 7: Build and flash**

```bash
source ~/esp/esp-idf-v5.5/export.sh && cd rd03d_uart && idf.py build && idf.py -p /dev/cu.usbmodem11101 flash
```

Expected: clean build (no warnings in web_server.c/main.c), flash OK.

- [x] **Step 8: Verify the page and the WebSocket headlessly**

```bash
curl -s --max-time 10 http://rd03d.local/ && echo
```

Expected: the placeholder HTML.

WebSocket check (scratchpad venv; create it if missing):

```bash
SP=/private/tmp/claude-501/-path-to-rd03d/1a58ef3a-b659-4aae-a07a-3f6d1a6f573b/scratchpad
[ -x $SP/venv/bin/python ] || python3 -m venv $SP/venv
$SP/venv/bin/pip install -q websockets && $SP/venv/bin/python -c "
import asyncio, websockets
async def main():
    async with websockets.connect('ws://rd03d.local/ws') as ws:
        for _ in range(5):
            print(await asyncio.wait_for(ws.recv(), timeout=5))
asyncio.run(main())
"
```

Expected: 5 JSON lines like `{"t":[{"x":-551,"y":550,"v":0},null,null],"dropped":0,"bad":0}` arriving at ~10/s. Run it twice to prove reconnect. Also capture ~8 s of console (pyserial snippet) and confirm `ws client connected` appears and `T1:` lines never stop.

- [x] **Step 9: Re-run host parser tests (regression)**

```bash
cd rd03d_uart/tests && cc -Wall -Wextra -o test_rd03d test_rd03d.c ../main/rd03d.c && ./test_rd03d
```

Expected: `all tests passed`

- [x] **Step 10: Commit**

```bash
git add rd03d_uart/main/web_server.h rd03d_uart/main/web_server.c rd03d_uart/main/index.html rd03d_uart/main/CMakeLists.txt rd03d_uart/main/main.c rd03d_uart/sdkconfig.defaults
git commit -m "feat(rd03d_uart): serve web page and push parsed frames over WebSocket"
```

---

### Task 5: The radar chart page

**Files:**
- Modify: `rd03d_uart/main/index.html` (replace placeholder entirely)

- [x] **Step 1: Write the chart page**

Replace `rd03d_uart/main/index.html` with:

```html
<!DOCTYPE html>
<html>
<head>
<meta charset="utf-8">
<meta name="viewport" content="width=device-width, initial-scale=1">
<title>RD-03D Radar</title>
<style>
  html, body { margin: 0; height: 100%; background: #121212; color: #ddd;
               font: 14px system-ui, sans-serif; overflow: hidden; }
  #hud { height: 56px; box-sizing: border-box; padding: 8px 12px;
         display: flex; flex-wrap: wrap; gap: 2px 18px; align-items: baseline; }
  #status { font-weight: 600; }
  .ok { color: #4cd47a; }
  .bad { color: #ff6b6b; }
  canvas { display: block; width: 100vw; height: calc(100vh - 56px);
           touch-action: none; }
</style>
</head>
<body>
<div id="hud">
  <span id="status" class="bad">connecting&hellip;</span>
  <span id="targets"></span>
  <span id="stats"></span>
</div>
<canvas id="chart"></canvas>
<script>
"use strict";
const RANGE_X_MM = 3000;  // +/-3 m across
const RANGE_Y_MM = 6000;  // 6 m forward
const TRAIL = 120;        // trail points per target
const COLORS = ["#00b4ff", "#00dc78", "#ffb428"];

const canvas = document.getElementById("chart");
const ctx = canvas.getContext("2d");
const statusEl = document.getElementById("status");
const targetsEl = document.getElementById("targets");
const statsEl = document.getElementById("stats");

let frames = 0;
let latest = [null, null, null];
const trails = [[], [], []];

function resize() {
  const dpr = window.devicePixelRatio || 1;
  canvas.width = Math.round(canvas.clientWidth * dpr);
  canvas.height = Math.round(canvas.clientHeight * dpr);
}
window.addEventListener("resize", resize);

// Uniform mm->px scale so range arcs stay circular.
function scale() {
  return Math.min(canvas.width / (2 * RANGE_X_MM), canvas.height / RANGE_Y_MM);
}

function toPx(xMm, yMm) {
  const s = scale();
  return [canvas.width / 2 + xMm * s, canvas.height - yMm * s];
}

function drawGrid() {
  ctx.clearRect(0, 0, canvas.width, canvas.height);
  const dpr = window.devicePixelRatio || 1;
  const [ox, oy] = toPx(0, 0);
  const s = scale();

  ctx.lineWidth = 1;
  ctx.strokeStyle = "#2c2c2c";
  ctx.fillStyle = "#666";
  ctx.font = (12 * dpr) + "px system-ui";

  for (let r = 1000; r <= RANGE_Y_MM; r += 1000) {
    ctx.beginPath();
    ctx.arc(ox, oy, r * s, Math.PI, 2 * Math.PI);
    ctx.stroke();
    ctx.fillText((r / 1000) + " m", ox + 6 * dpr, oy - r * s - 4 * dpr);
  }

  ctx.strokeStyle = "#3a3a3a";
  ctx.beginPath();
  ctx.moveTo(ox, oy); ctx.lineTo(ox, oy - RANGE_Y_MM * s);
  ctx.moveTo(ox - RANGE_X_MM * s, oy); ctx.lineTo(ox + RANGE_X_MM * s, oy);
  ctx.stroke();
}

function render() {
  drawGrid();
  const dpr = window.devicePixelRatio || 1;
  for (let i = 0; i < 3; i++) {
    ctx.fillStyle = COLORS[i];
    const tr = trails[i];
    for (let j = 0; j < tr.length; j++) {
      const [px, py] = toPx(tr[j].x, tr[j].y);
      ctx.globalAlpha = 0.1 + 0.3 * ((j + 1) / tr.length);
      ctx.beginPath();
      ctx.arc(px, py, 2.5 * dpr, 0, 7);
      ctx.fill();
    }
    ctx.globalAlpha = 1;
    if (latest[i]) {
      const [px, py] = toPx(latest[i].x, latest[i].y);
      ctx.beginPath();
      ctx.arc(px, py, 6 * dpr, 0, 7);
      ctx.fill();
    }
  }
  requestAnimationFrame(render);
}

function onMessage(ev) {
  let msg;
  try { msg = JSON.parse(ev.data); } catch (e) { return; }
  frames++;
  latest = msg.t;
  for (let i = 0; i < 3; i++) {
    if (msg.t[i]) {
      trails[i].push({ x: msg.t[i].x, y: msg.t[i].y });
      if (trails[i].length > TRAIL) trails[i].shift();
    }
  }
  statsEl.textContent =
    "frames " + frames + " · dropped " + msg.dropped + " · bad " + msg.bad;
  targetsEl.innerHTML = msg.t.map(function (t, i) {
    return t
      ? '<span style="color:' + COLORS[i] + '">T' + (i + 1) +
        " x=" + t.x + " y=" + t.y + " v=" + t.v + "</span>"
      : '<span style="color:#555">T' + (i + 1) + " —</span>";
  }).join(" ");
}

function connect() {
  const ws = new WebSocket("ws://" + location.host + "/ws");
  ws.onopen = function () {
    statusEl.textContent = "connected";
    statusEl.className = "ok";
  };
  ws.onclose = function () {
    statusEl.textContent = "disconnected — retrying";
    statusEl.className = "bad";
    setTimeout(connect, 2000);
  };
  ws.onerror = function () { ws.close(); };
  ws.onmessage = onMessage;
}

resize();
connect();
render();
</script>
</body>
</html>
```

- [x] **Step 2: Build and flash**

```bash
source ~/esp/esp-idf-v5.5/export.sh && cd rd03d_uart && idf.py build && idf.py -p /dev/cu.usbmodem11101 flash
```

Expected: clean build, flash OK.

- [x] **Step 3: Headless sanity**

```bash
curl -s --max-time 10 http://rd03d.local/ | head -8
```

Expected: the new page's opening HTML (doctype, title "RD-03D Radar"). Then rerun the Task 4 Step 8 WebSocket check once — still 5 JSON lines.

- [x] **Step 4: Browser verification (user at the keyboard)**

Open `http://rd03d.local` on the Mac. Expected: dark page, range arcs, HUD flips to green "connected", colored dot(s) tracking motion with fading trails, per-target readout updating ~10/s. Pull XIAO power → HUD shows "disconnected — retrying"; restore → recovers by itself. Then open the same URL on a phone on the same WiFi alongside the Mac — both update live.

The implementing agent verifies what it can headlessly and hands the visual check to the controller/user, reporting DONE_WITH_CONCERNS if unconfirmed.

- [x] **Step 5: Commit**

```bash
git add rd03d_uart/main/index.html
git commit -m "feat(rd03d_uart): live radar chart web page"
```

---

### Task 6: Docs + untethered verification

**Files:**
- Modify: `rd03d_uart/README.md`
- Modify: `RD03D_RadarChart/README.md`

- [x] **Step 1: Update rd03d_uart/README.md**

In `rd03d_uart/README.md`, after the "## Output" section, add:

```markdown
## WiFi + web UI

The firmware joins the WiFi network configured via `idf.py menuconfig`
(*RD03D Configuration* → SSID/password; stored only in the untracked
`sdkconfig`, 2.4 GHz WPA2 networks only) and serves a live radar chart:

- Open **http://rd03d.local** from any browser on the same network (Mac or
  phone). The page shows targets on an XY chart with trails, plus link stats.
- Data path: `GET /ws` WebSocket pushes one JSON message per radar frame,
  e.g. `{"t":[{"x":-551,"y":550,"v":0},null,null],"dropped":0,"bad":0}`
  (x/y in mm, v in cm/s, absent targets `null`).
- At boot the firmware puts the radar in multi-target mode itself; viewers
  never send radar commands.
- Untethered use: power the XIAO from a USB power bank; the USB console is
  optional diagnostics only.
```

- [x] **Step 2: Update RD03D_RadarChart/README.md**

At the top of `RD03D_RadarChart/README.md`, after the title line, add:

```markdown
> **Note:** for WiFi viewing, the `../rd03d_uart` firmware now serves its own
> live chart at http://rd03d.local — no Processing needed. This sketch remains
> useful for direct USB-serial connections to the radar.
```

- [ ] **Step 3: Untethered test (user)**

Power the XIAO from a USB power bank at the radar's intended mounting spot (no
data cable) and open `http://rd03d.local` on Mac or phone. Expected: live
targets as before. This is a user-performed check; the agent reports it as
pending user confirmation.

- [x] **Step 4: Commit**

```bash
git add rd03d_uart/README.md RD03D_RadarChart/README.md
git commit -m "docs(rd03d_uart): document WiFi web UI; point RadarChart README at it"
```
